ManuelaDragic/sketchingWithHardware/content/posts/pictures/applekalender.png

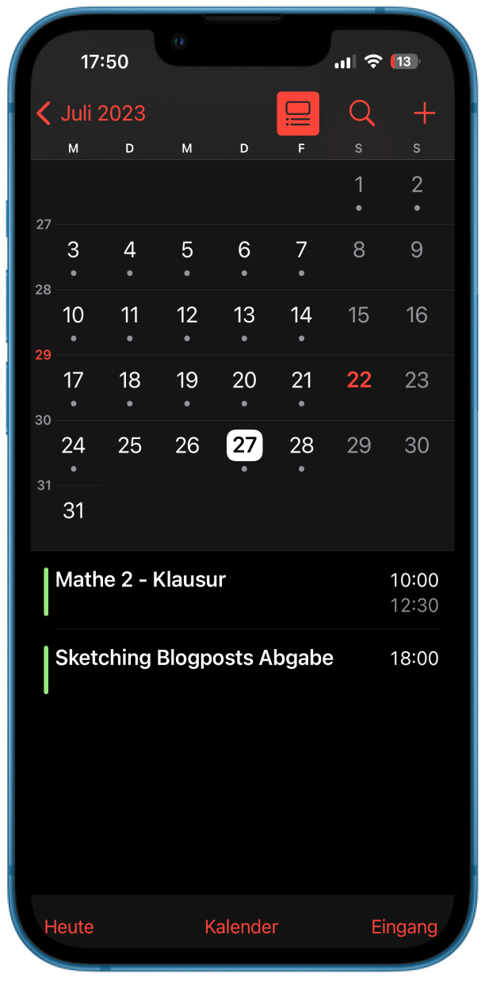
content/posts/pictures/applekalender.png
