ManuelaDragic/sketchingWithHardware/content/posts/pictures/bauteile.jpeg

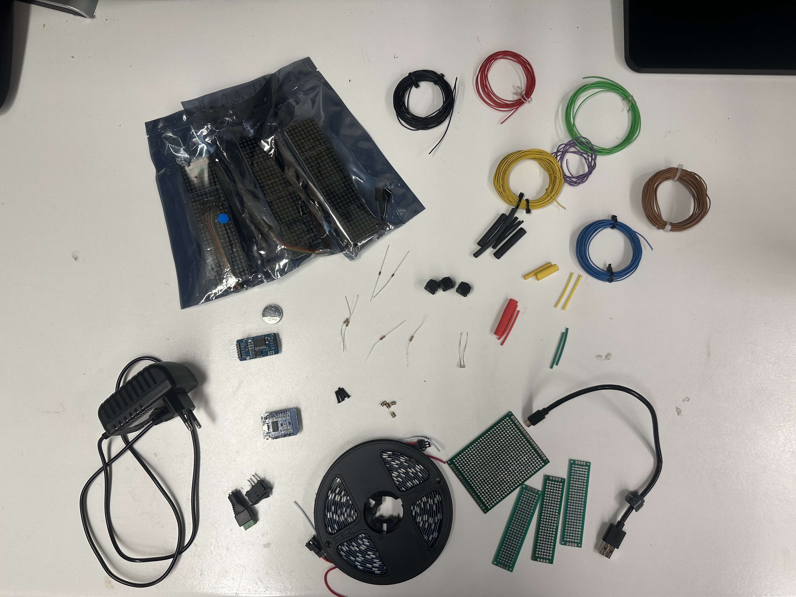
content/posts/pictures/bauteile.jpeg
