ManuelaDragic/sketchingWithHardware/content/posts/pictures/bereitstellen.png

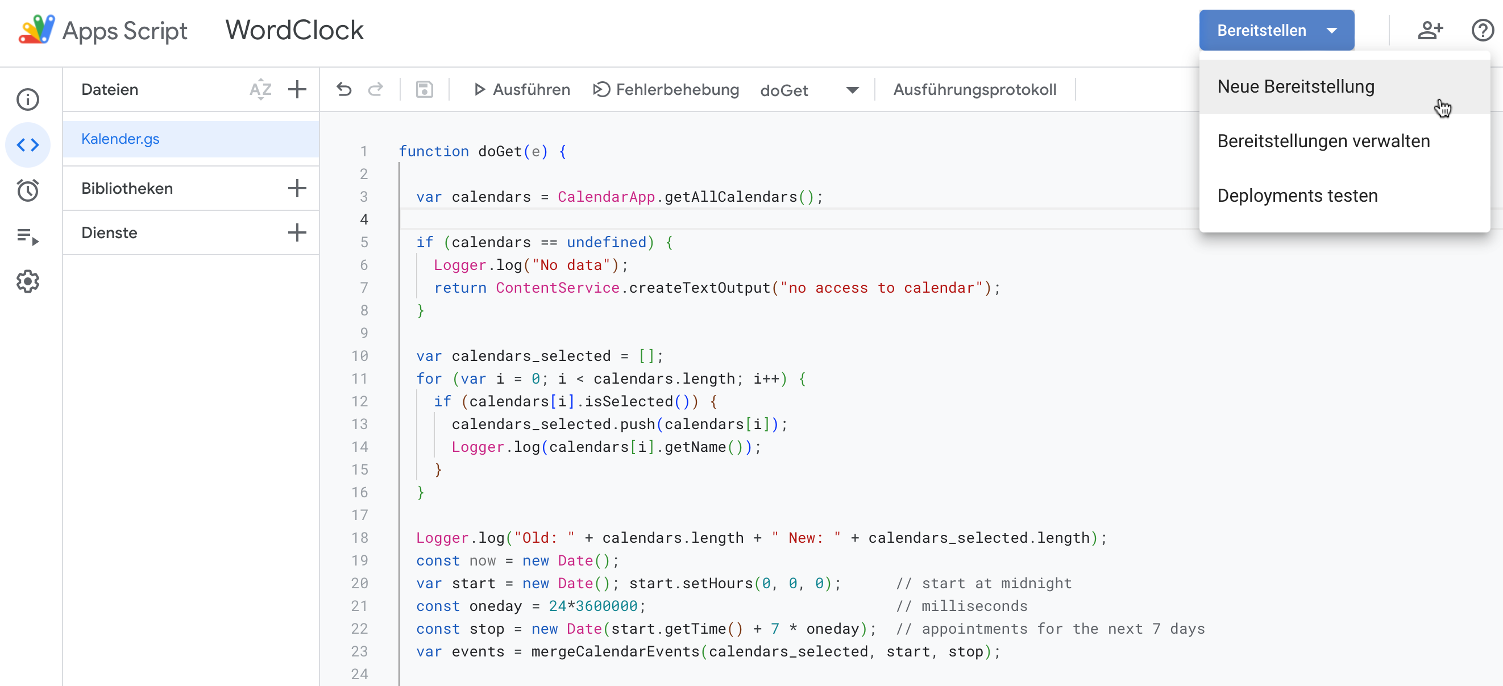
content/posts/pictures/bereitstellen.png
