ManuelaDragic/sketchingWithHardware/content/posts/pictures/boardauswahl.png

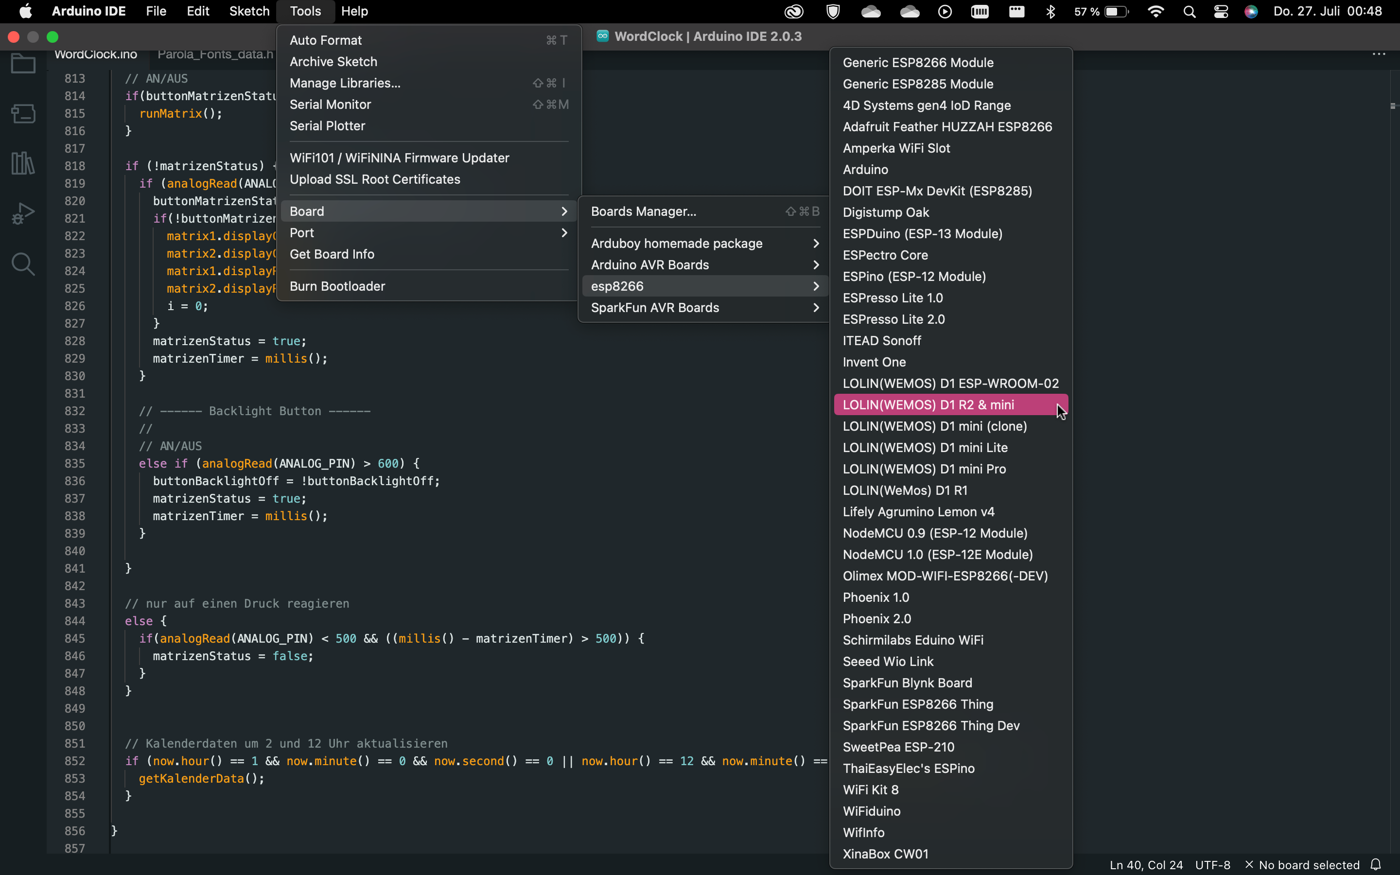
content/posts/pictures/boardauswahl.png
