ManuelaDragic/sketchingWithHardware/content/posts/pictures/boardmanager.png

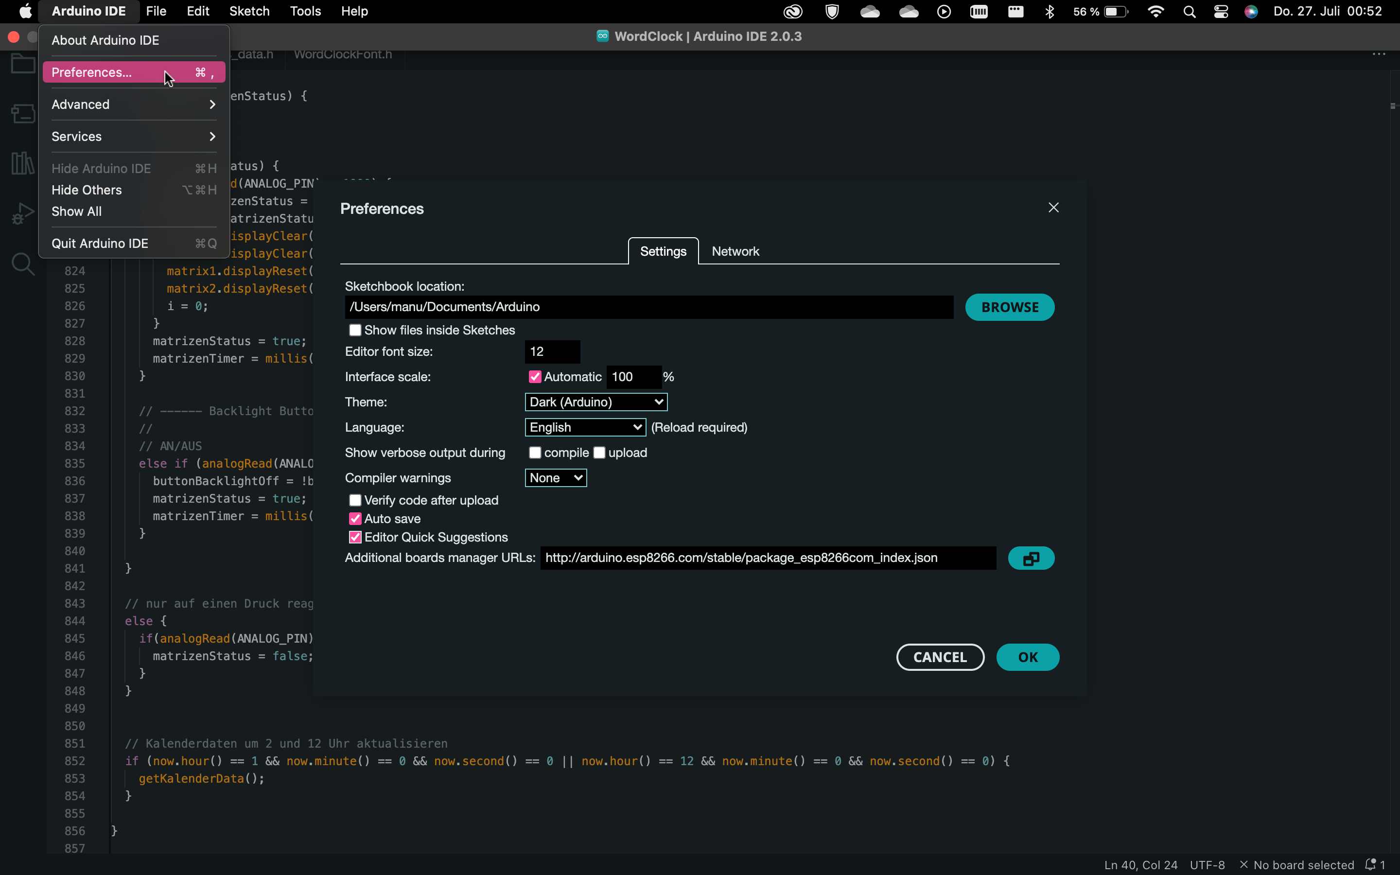
content/posts/pictures/boardmanager.png
