ManuelaDragic/sketchingWithHardware/content/posts/pictures/clock.jpeg

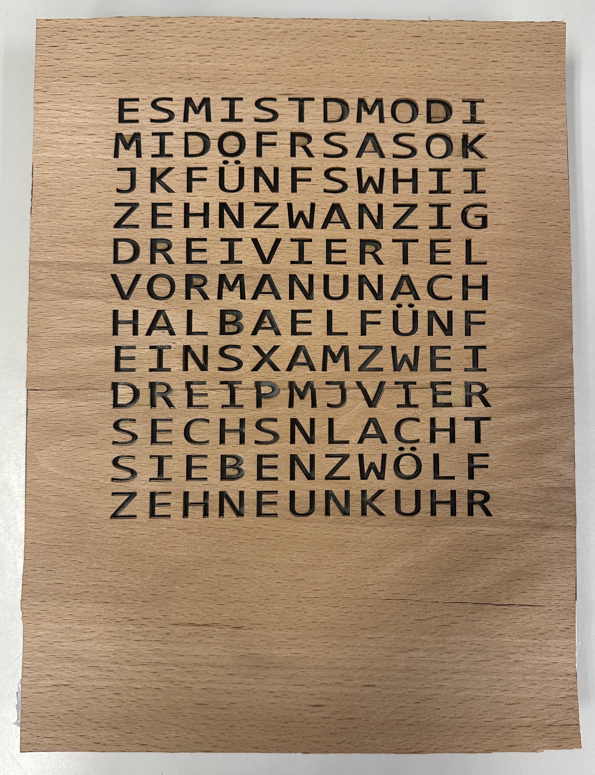
content/posts/pictures/clock.jpeg
