ManuelaDragic/sketchingWithHardware/content/posts/pictures/Code.png

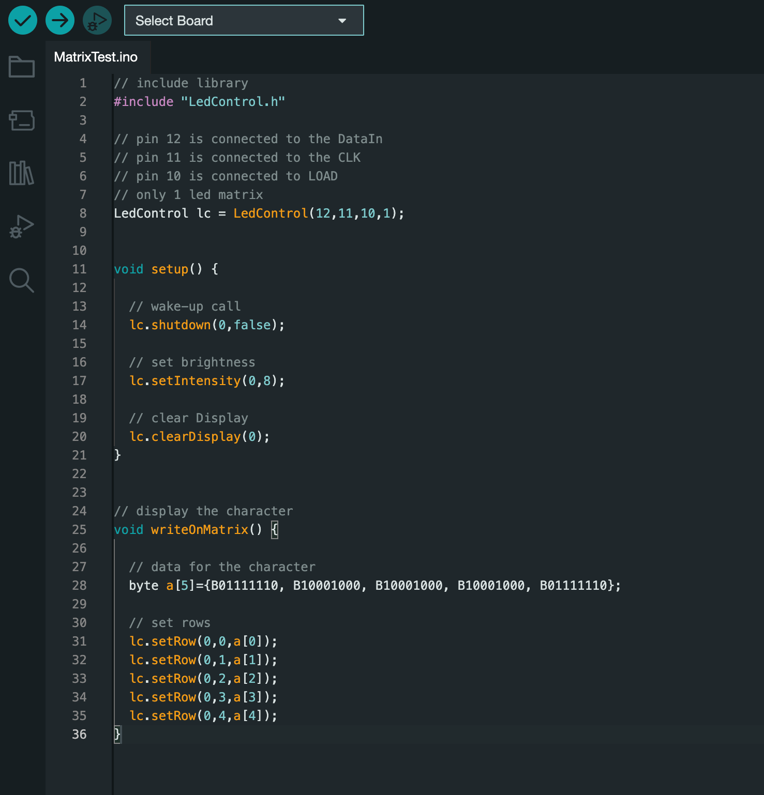
content/posts/pictures/Code.png
