ManuelaDragic/sketchingWithHardware/content/posts/pictures/druck.jpeg

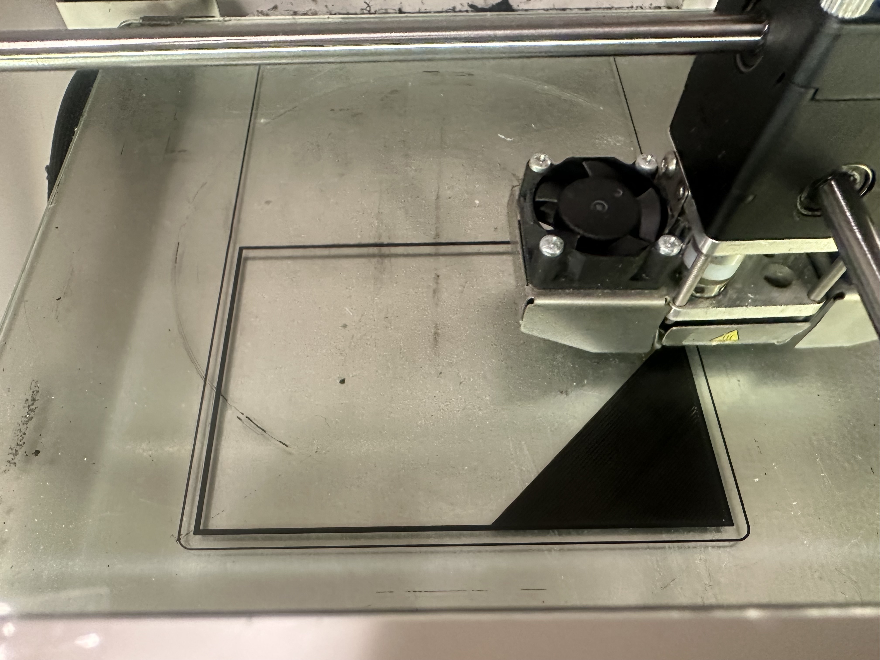
content/posts/pictures/druck.jpeg
