ManuelaDragic/sketchingWithHardware/content/posts/pictures/druck_durchsichtig.jpeg

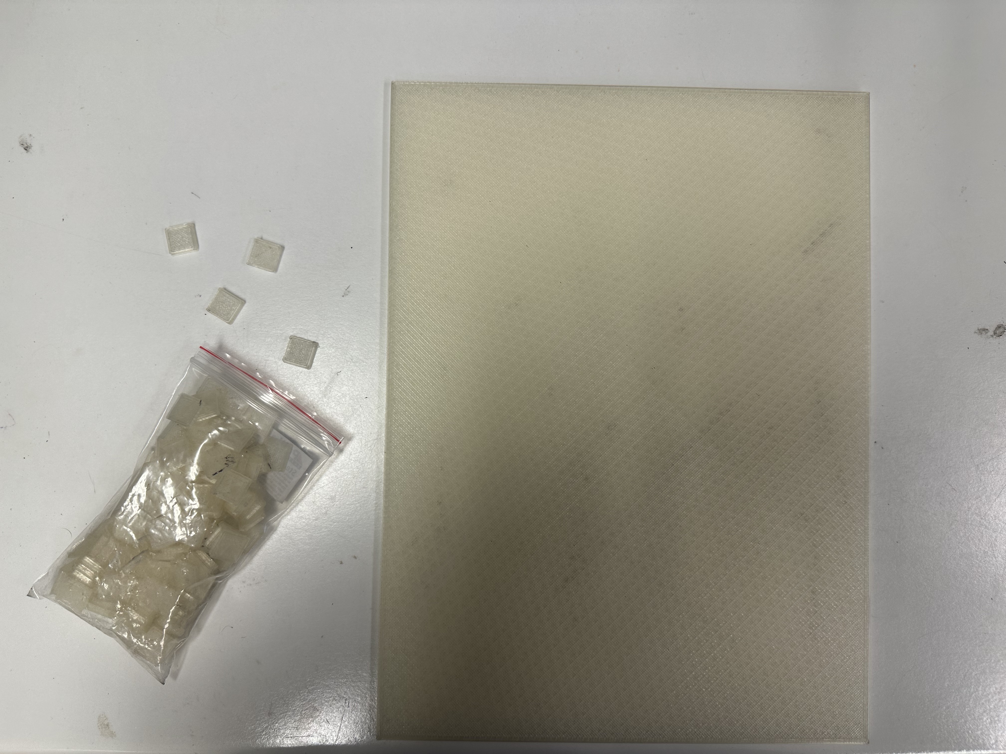
content/posts/pictures/druck_durchsichtig.jpeg
