ManuelaDragic/sketchingWithHardware/content/posts/pictures/Drucker.jpeg

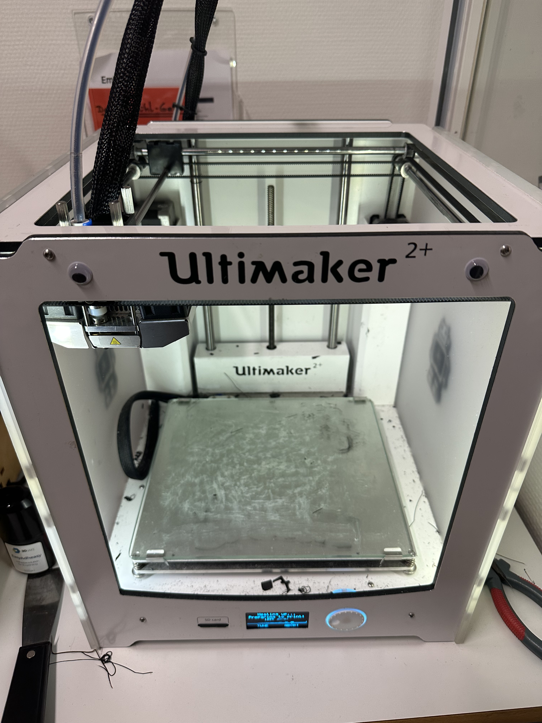
content/posts/pictures/Drucker.jpeg
