ManuelaDragic/sketchingWithHardware/content/posts/pictures/font.png

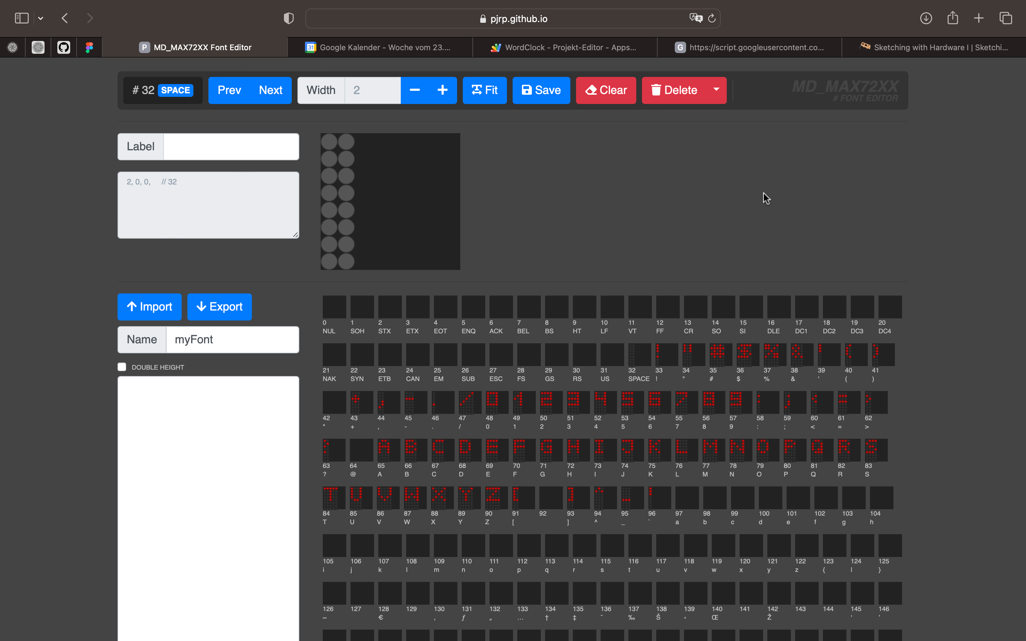
content/posts/pictures/font.png
