ManuelaDragic/sketchingWithHardware/content/posts/pictures/Gehaeuse.jpeg

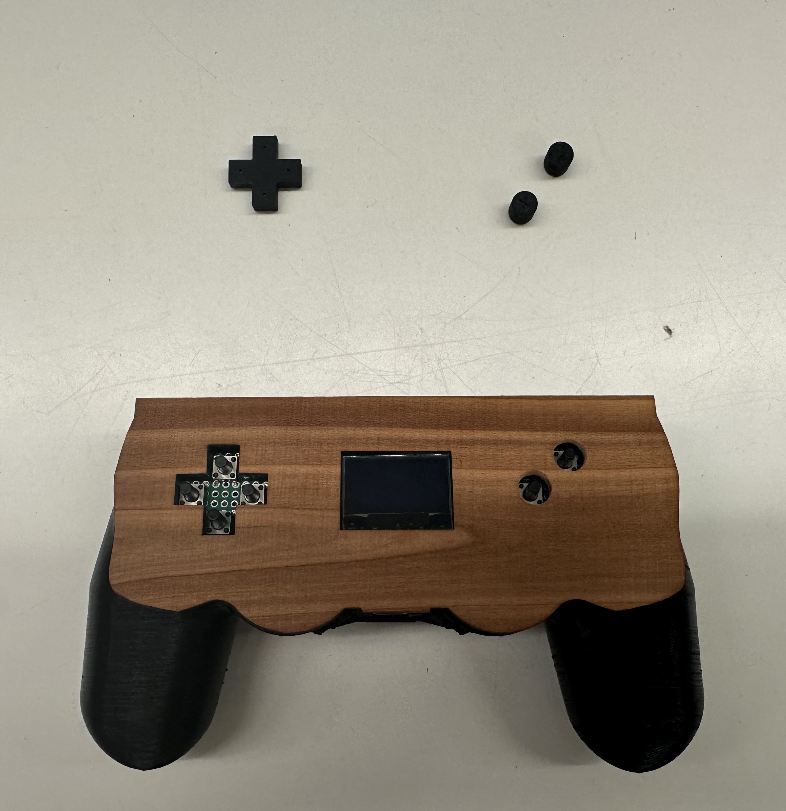
content/posts/pictures/Gehaeuse.jpeg
