ManuelaDragic/sketchingWithHardware/content/posts/pictures/Getriebe.jpeg

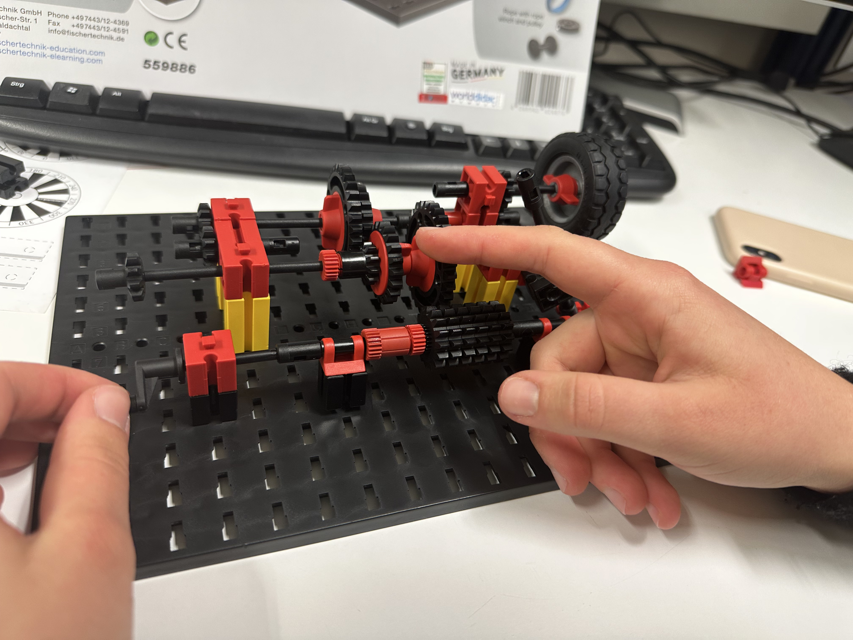
content/posts/pictures/Getriebe.jpeg
