ManuelaDragic/sketchingWithHardware/content/posts/pictures/hinten.png

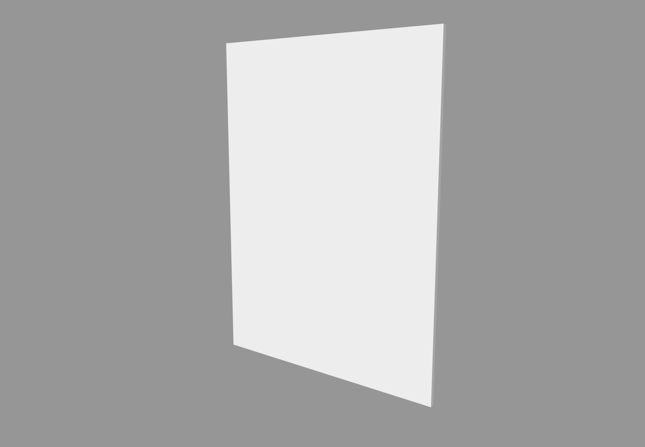
content/posts/pictures/hinten.png
