ManuelaDragic/sketchingWithHardware/content/posts/pictures/Interrupts.png

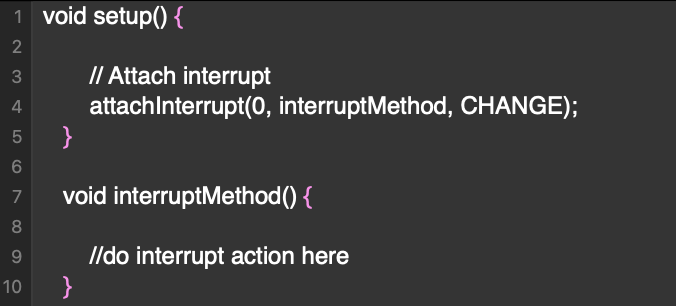
content/posts/pictures/Interrupts.png
