ManuelaDragic/sketchingWithHardware/content/posts/pictures/kalender_abonnieren.png

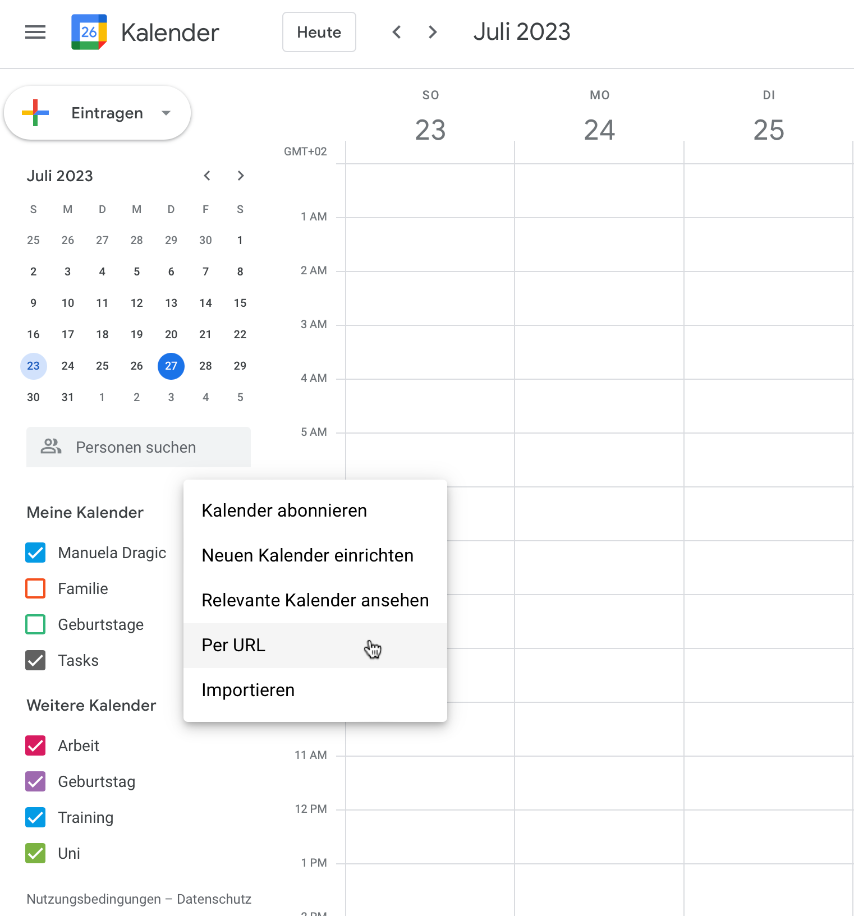
content/posts/pictures/kalender_abonnieren.png
