ManuelaDragic/sketchingWithHardware/content/posts/pictures/kalender_desktop.png

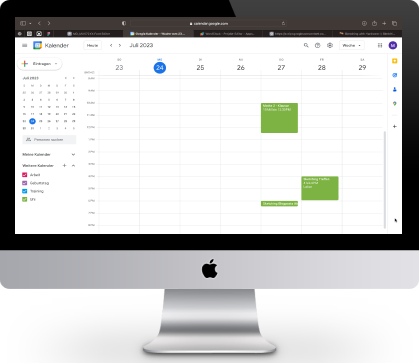
content/posts/pictures/kalender_desktop.png
