ManuelaDragic/sketchingWithHardware/content/posts/pictures/kalenderdaten2.png

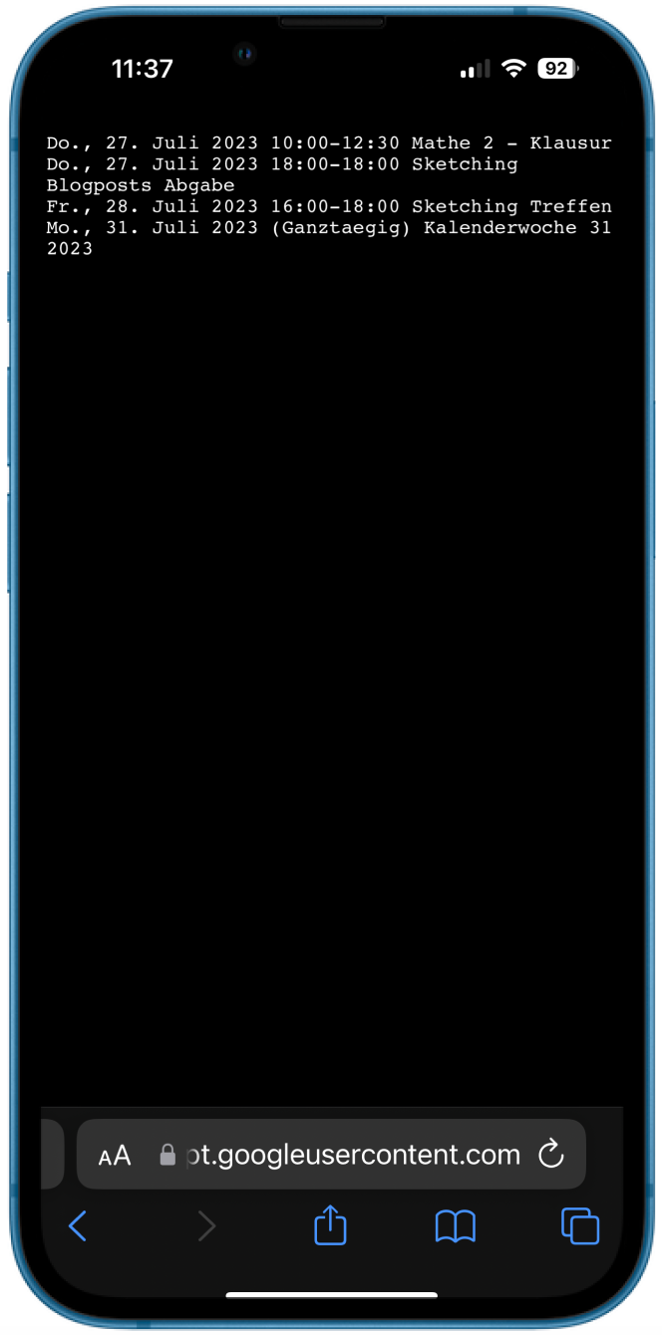
content/posts/pictures/kalenderdaten2.png
