ManuelaDragic/sketchingWithHardware/content/posts/pictures/kalenderdaten_desktop.png

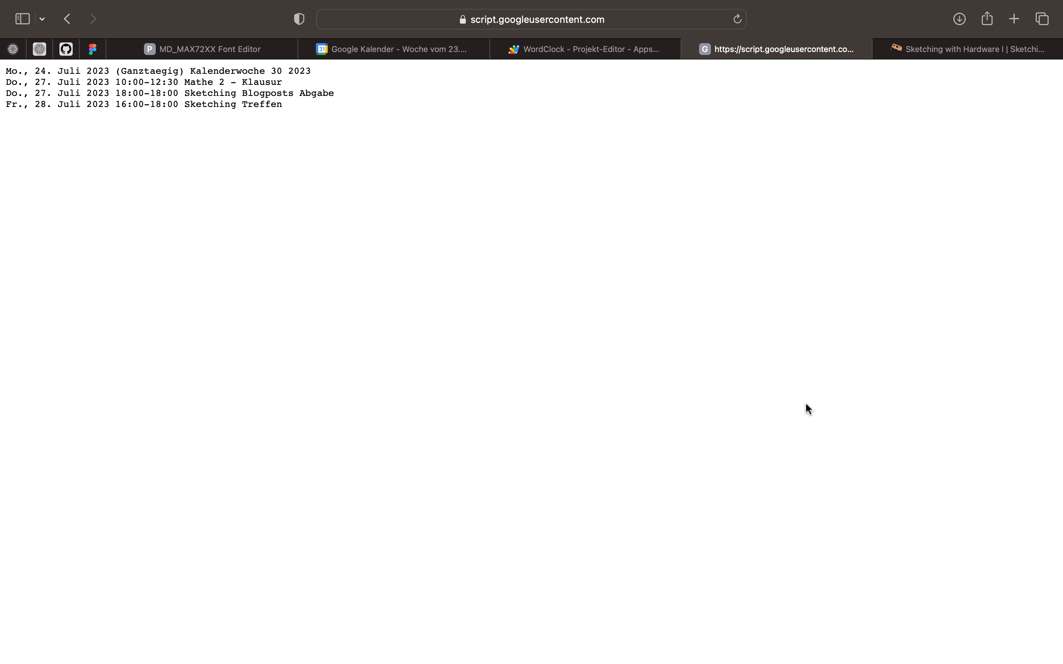
content/posts/pictures/kalenderdaten_desktop.png
