ManuelaDragic/sketchingWithHardware/content/posts/pictures/led_halterung.jpeg

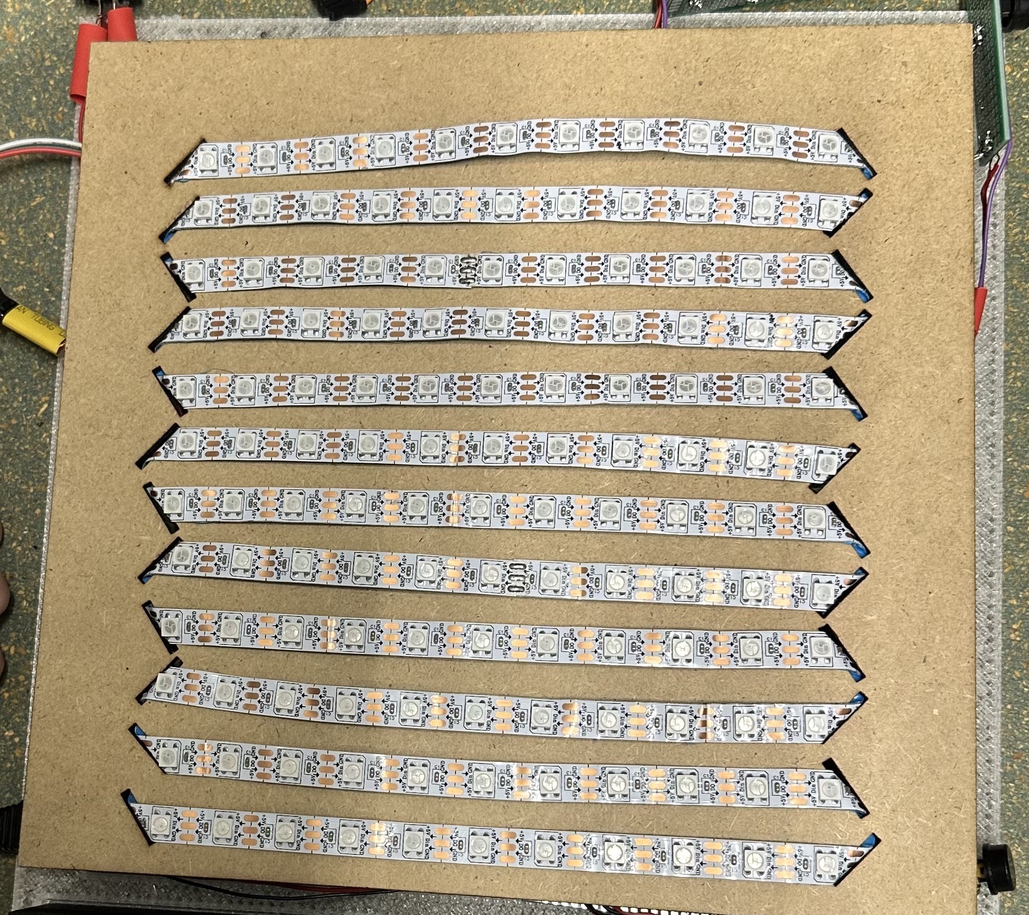
content/posts/pictures/led_halterung.jpeg
