ManuelaDragic/sketchingWithHardware/content/posts/pictures/libraries.png

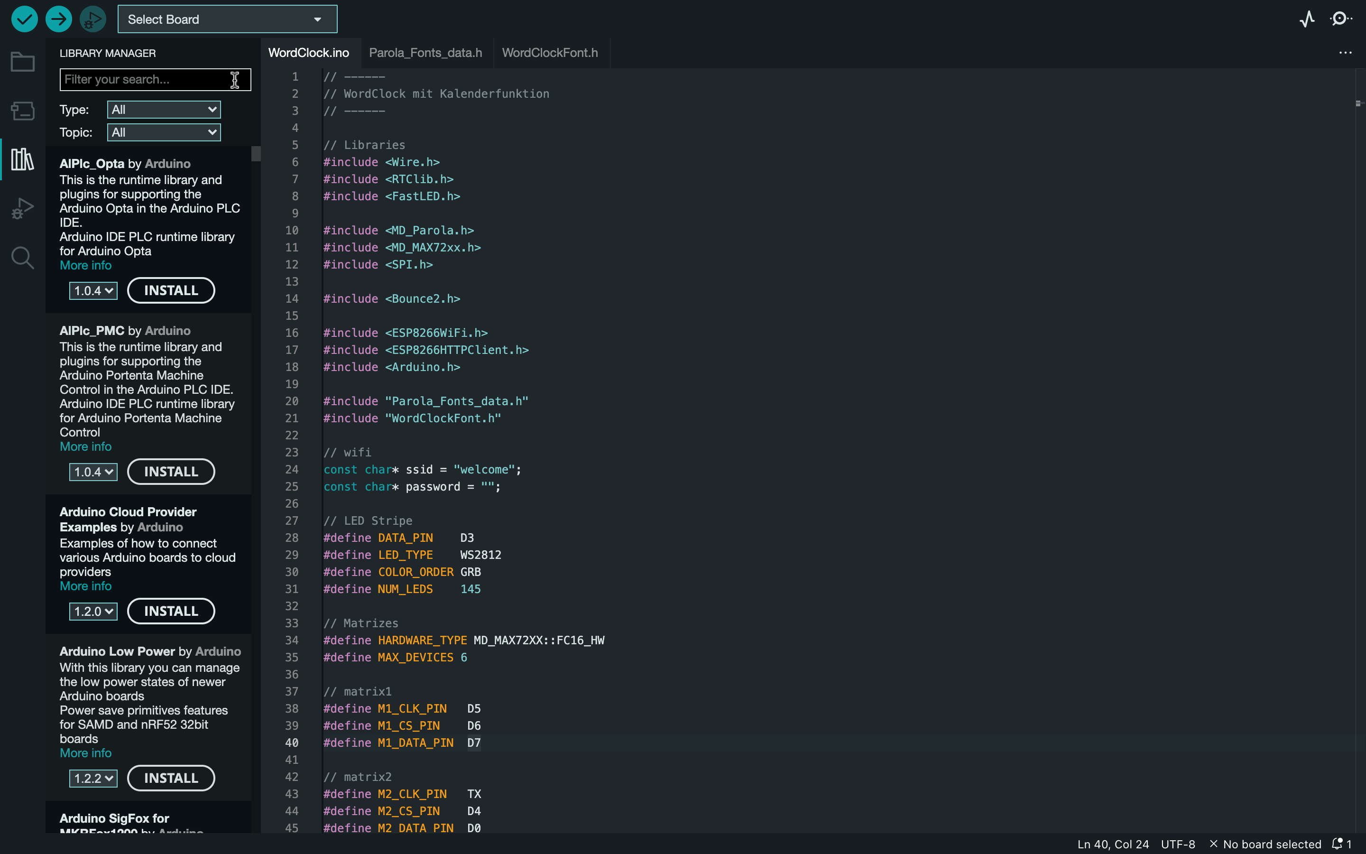
content/posts/pictures/libraries.png
