ManuelaDragic/sketchingWithHardware/content/posts/pictures/Lightburn.png

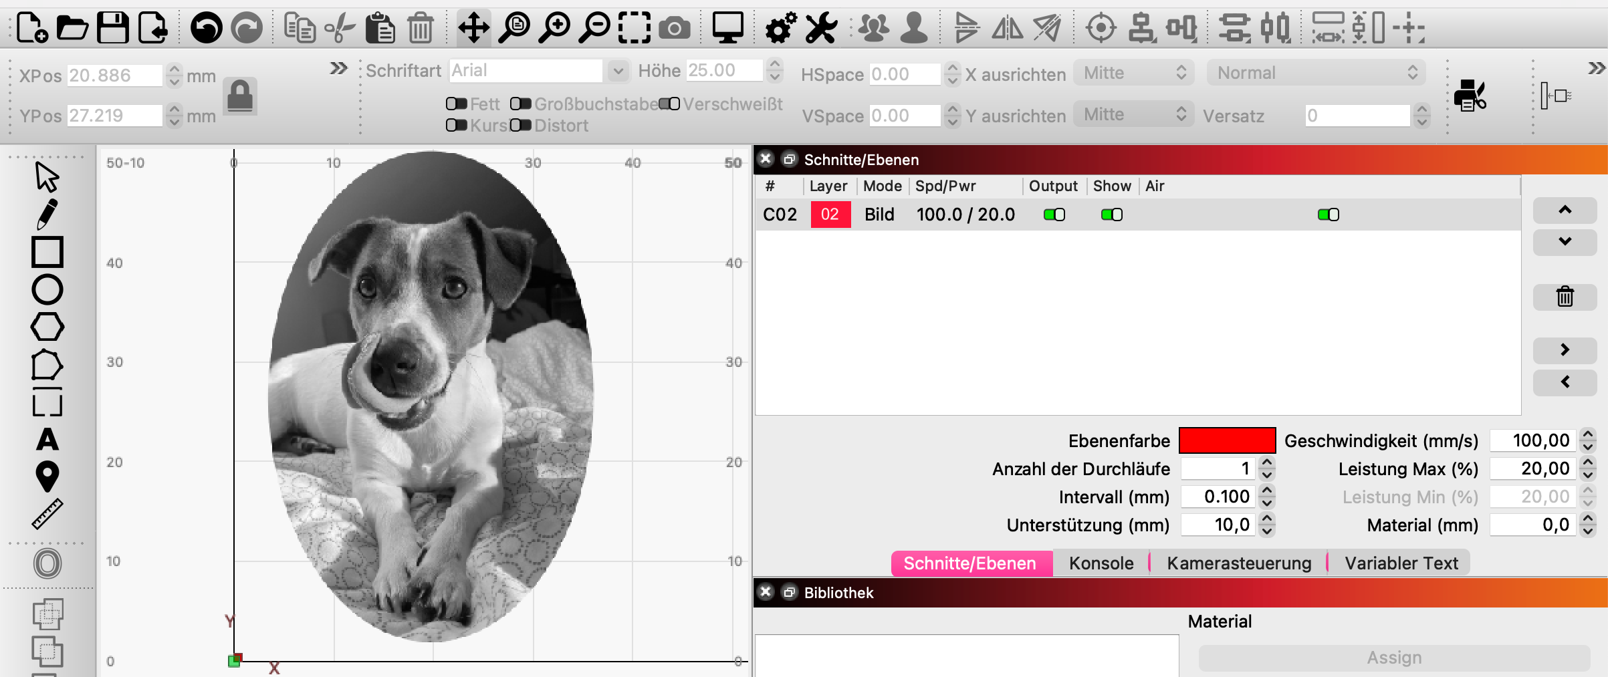
content/posts/pictures/Lightburn.png
