ManuelaDragic/sketchingWithHardware/content/posts/pictures/link.png

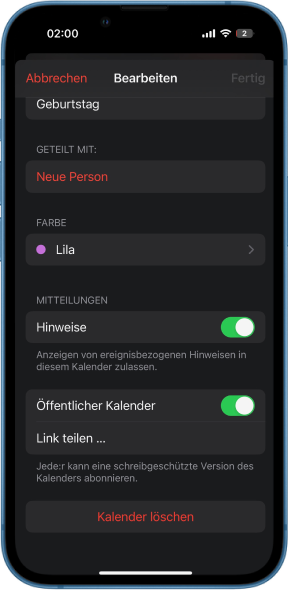
content/posts/pictures/link.png
