ManuelaDragic/sketchingWithHardware/content/posts/pictures/loeten1.png

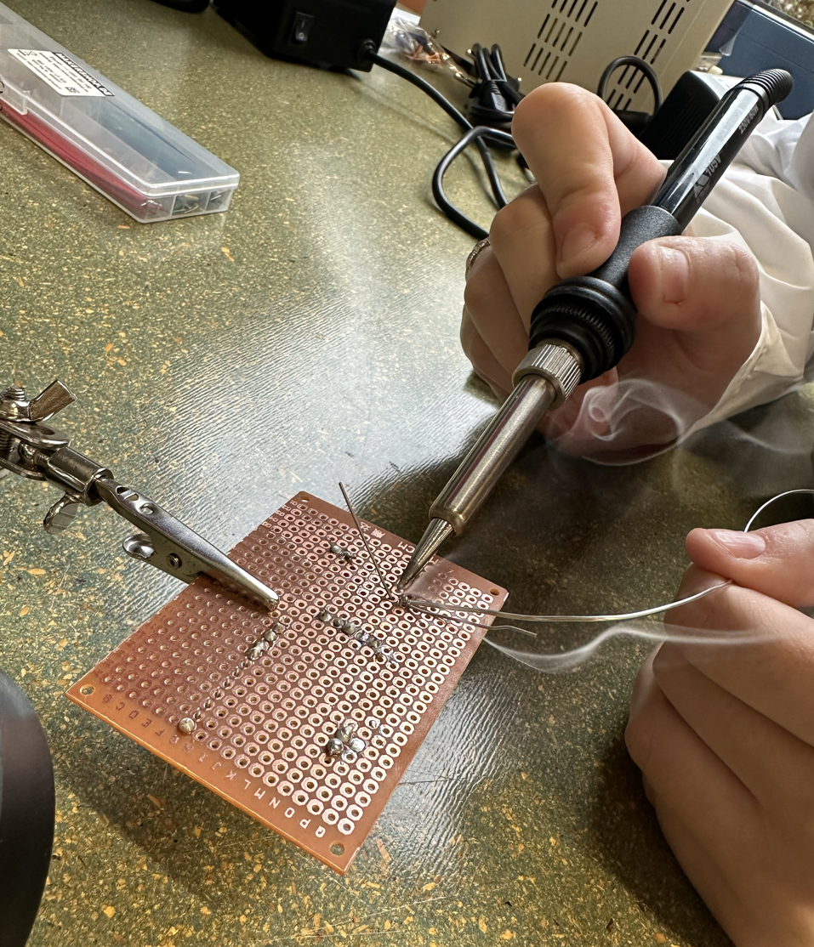
content/posts/pictures/loeten1.png
