ManuelaDragic/sketchingWithHardware/content/posts/pictures/loeten2.png

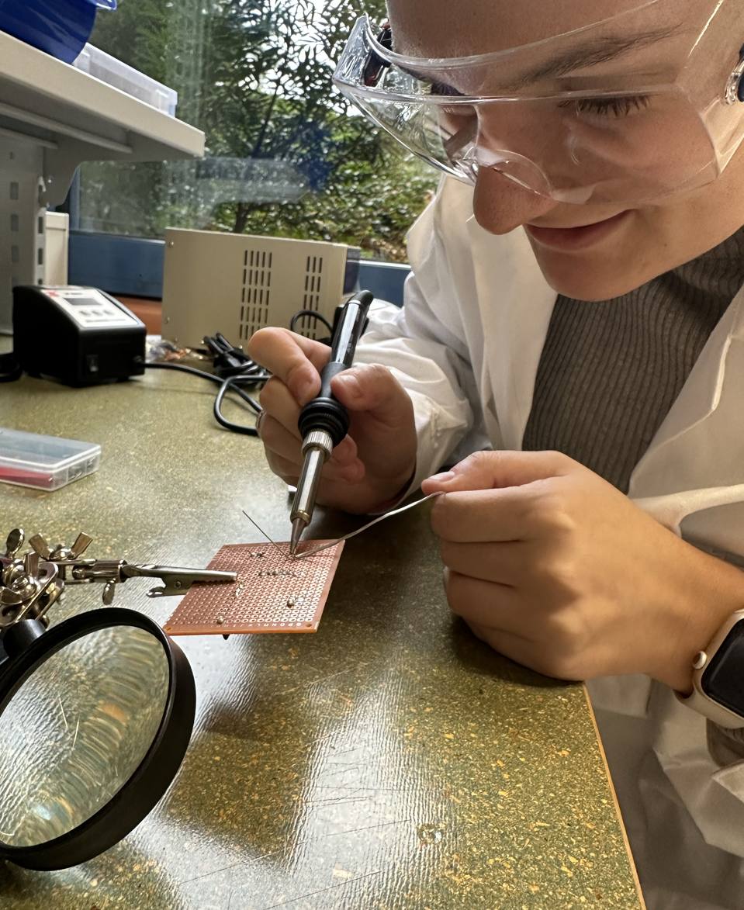
content/posts/pictures/loeten2.png
