ManuelaDragic/sketchingWithHardware/content/posts/pictures/loetplan.jpg

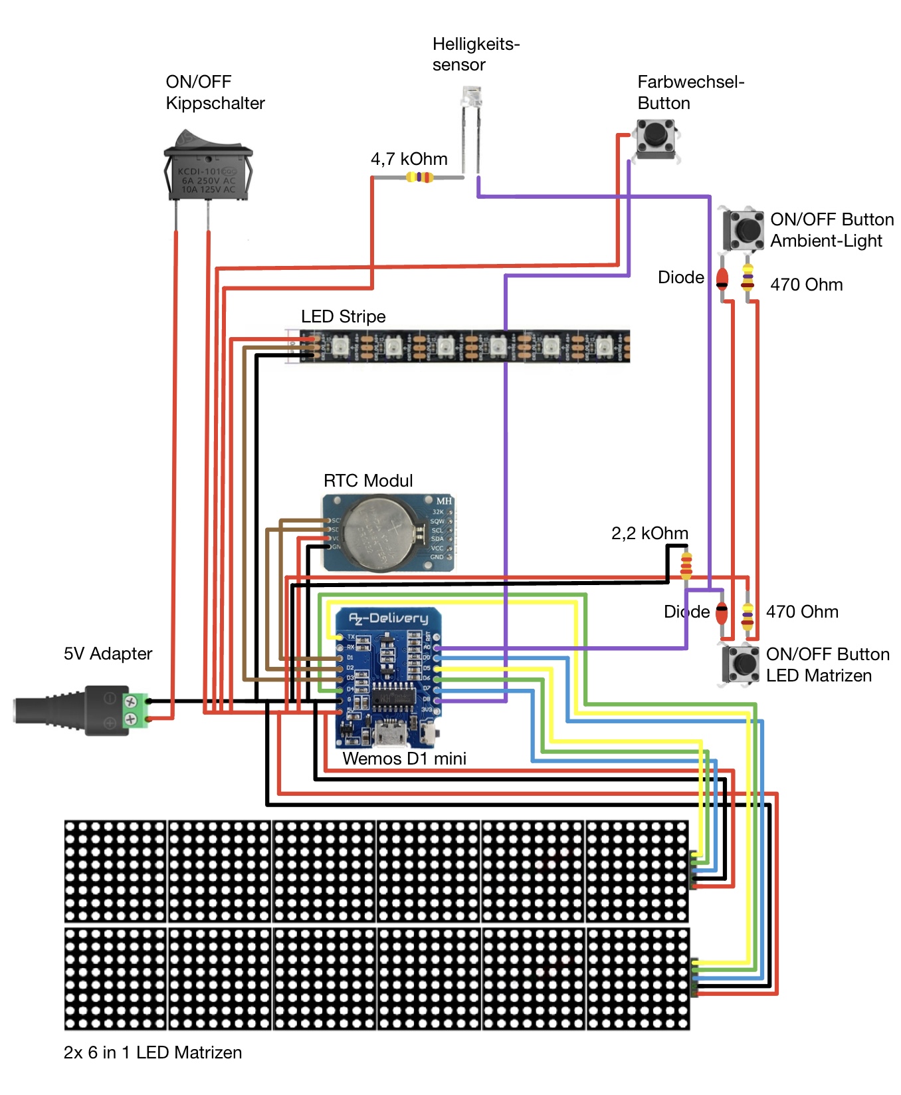
content/posts/pictures/loetplan.jpg
