ManuelaDragic/sketchingWithHardware/content/posts/pictures/loetzubehoer.png

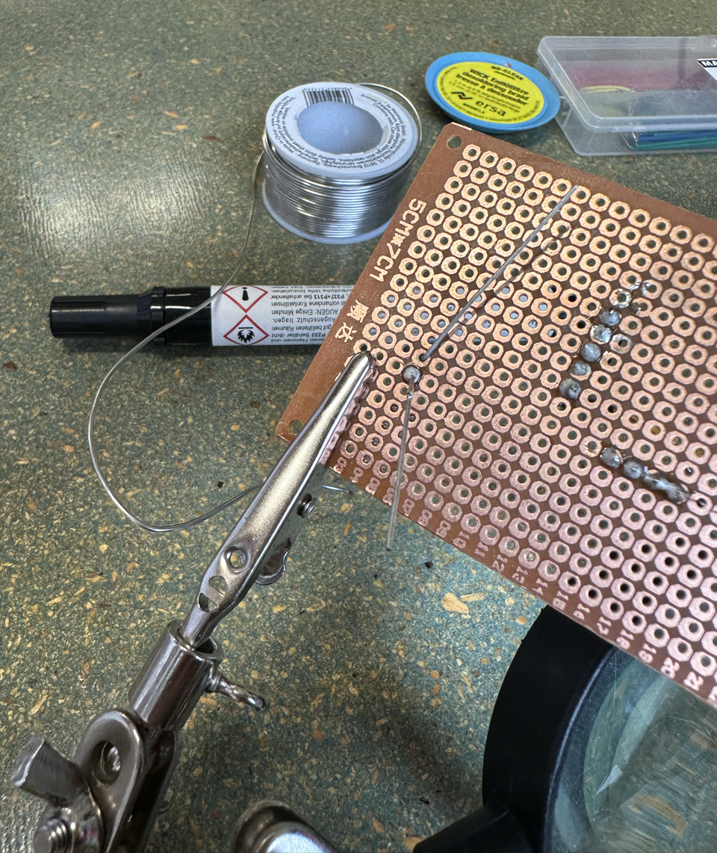
content/posts/pictures/loetzubehoer.png
