ManuelaDragic/sketchingWithHardware/content/posts/pictures/matrizenhalterung.png

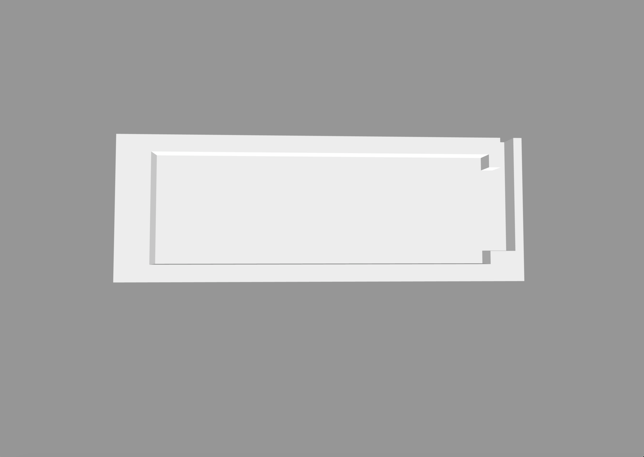
content/posts/pictures/matrizenhalterung.png
