ManuelaDragic/sketchingWithHardware/content/posts/pictures/Messung.png

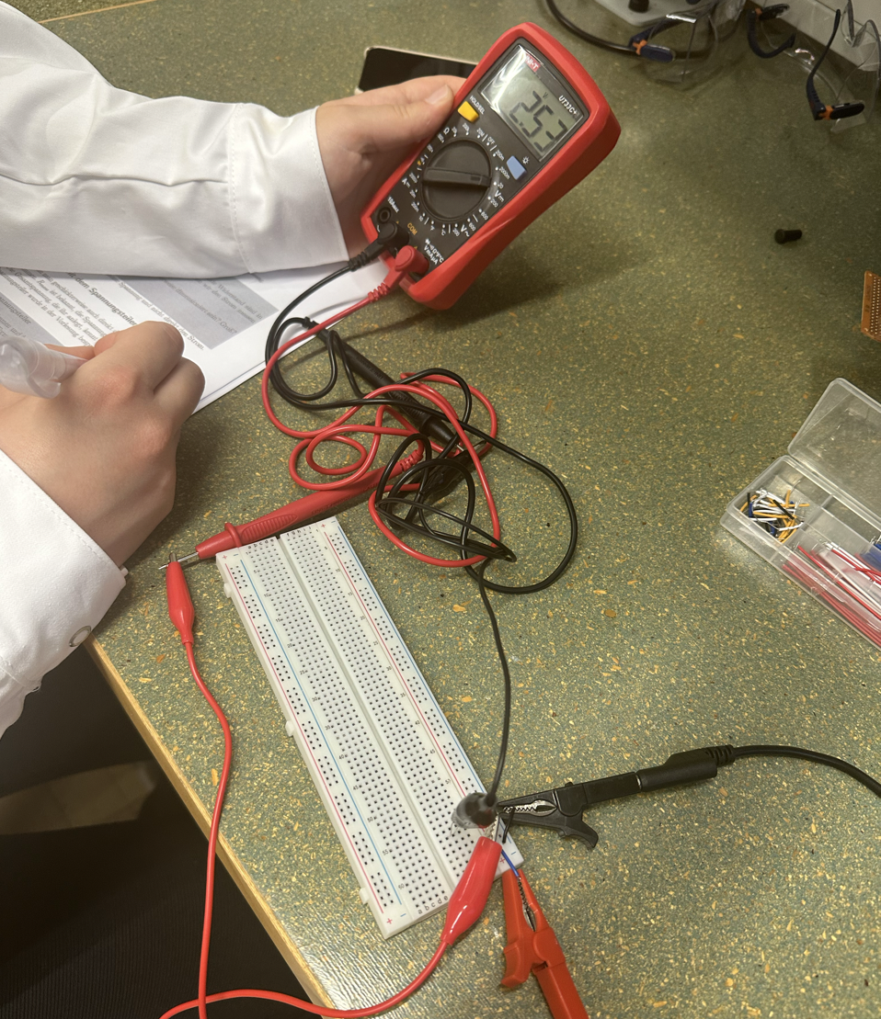
content/posts/pictures/Messung.png
