ManuelaDragic/sketchingWithHardware/content/posts/pictures/Messwerte.png

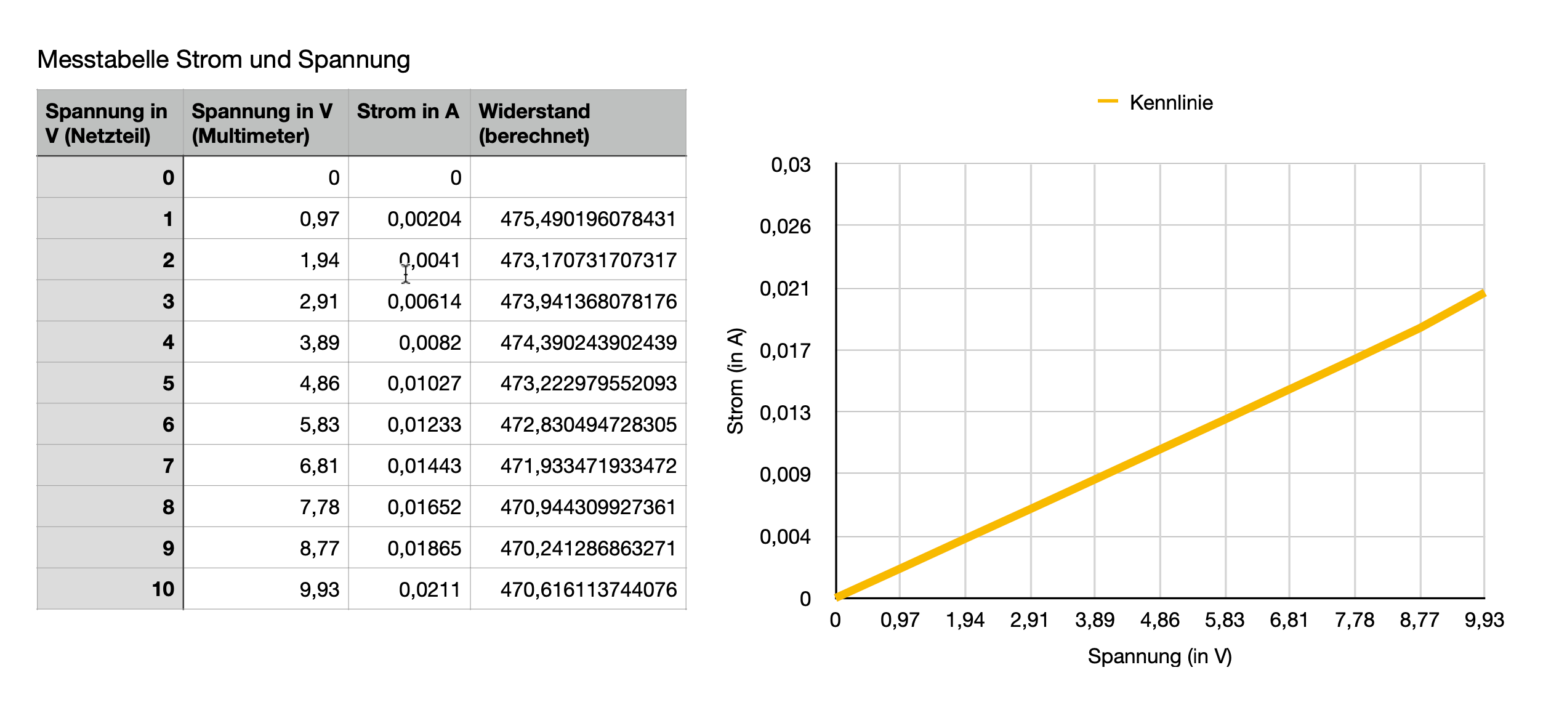
content/posts/pictures/Messwerte.png
