ManuelaDragic/sketchingWithHardware/content/posts/pictures/neuesProjekt.png

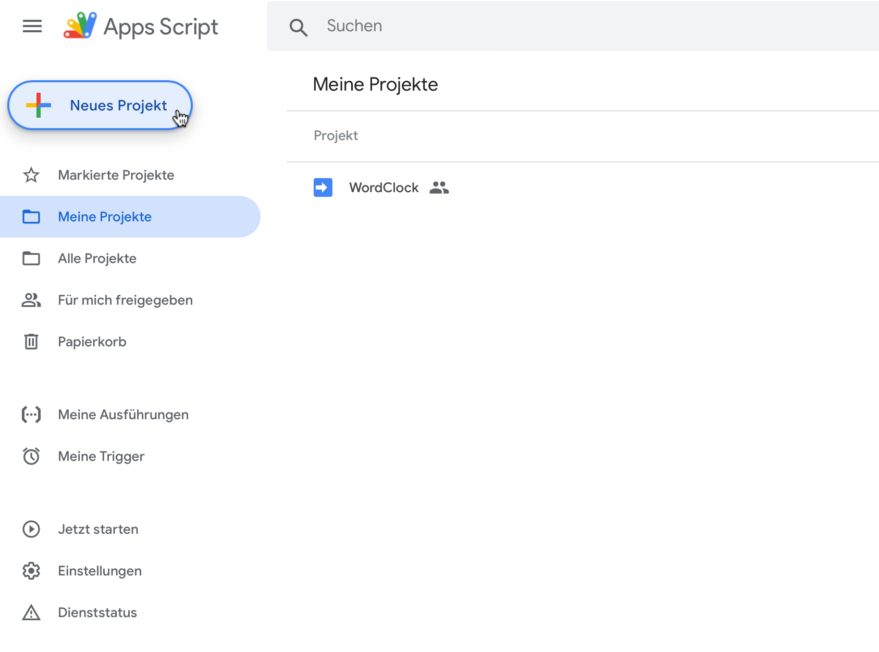
content/posts/pictures/neuesProjekt.png
