ManuelaDragic/sketchingWithHardware/content/posts/pictures/offen.jpeg

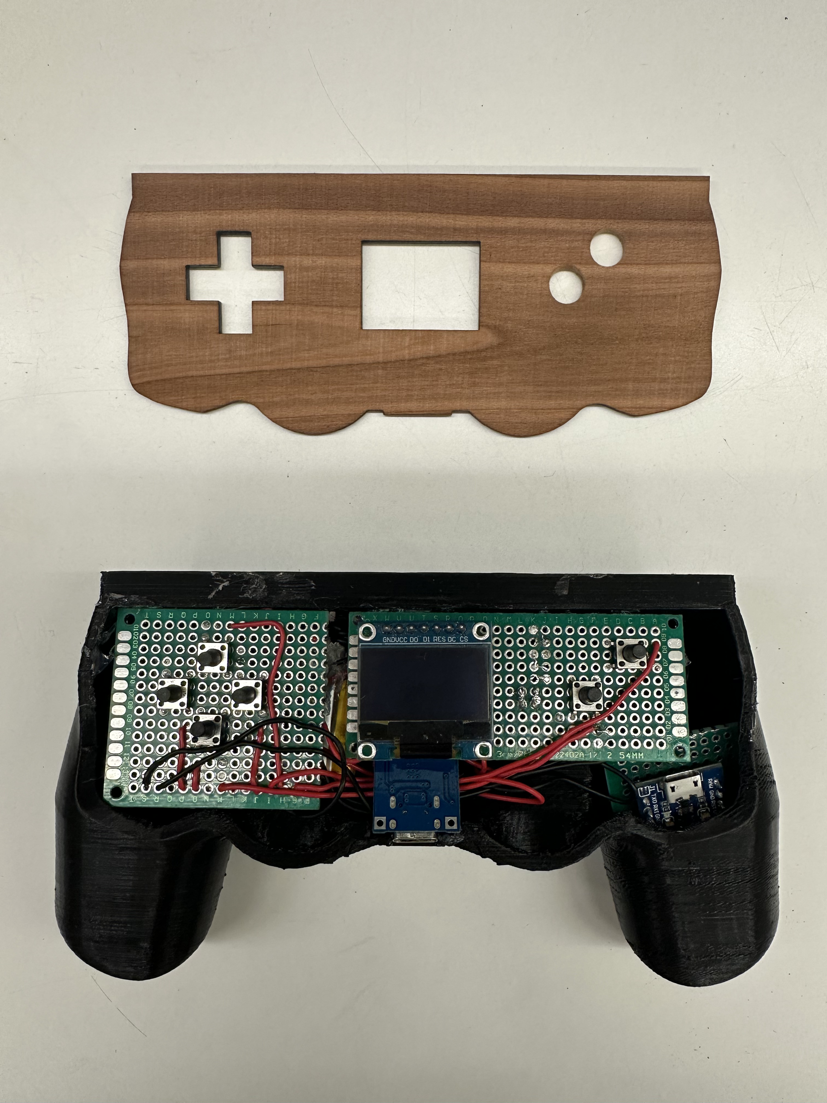
content/posts/pictures/offen.jpeg
