ManuelaDragic/sketchingWithHardware/content/posts/pictures/Planetengetriebe.jpeg

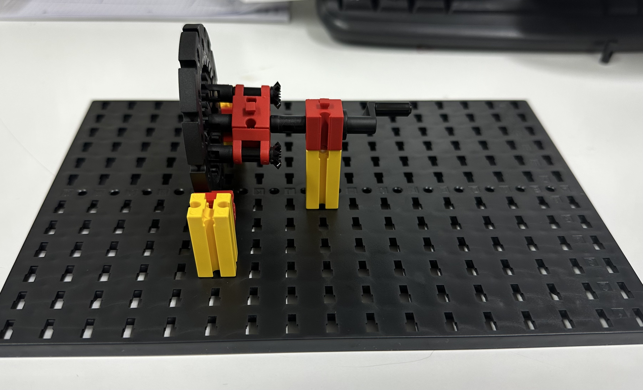
content/posts/pictures/Planetengetriebe.jpeg
