ManuelaDragic/sketchingWithHardware/content/posts/pictures/platte.jpeg

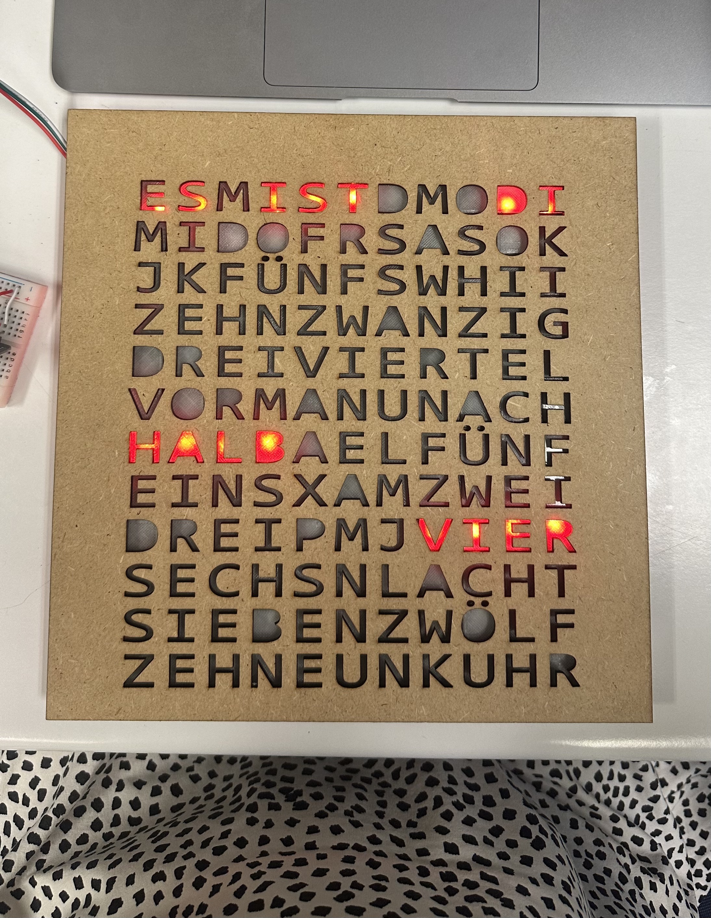
content/posts/pictures/platte.jpeg
