ManuelaDragic/sketchingWithHardware/content/posts/pictures/projektpitch2.png

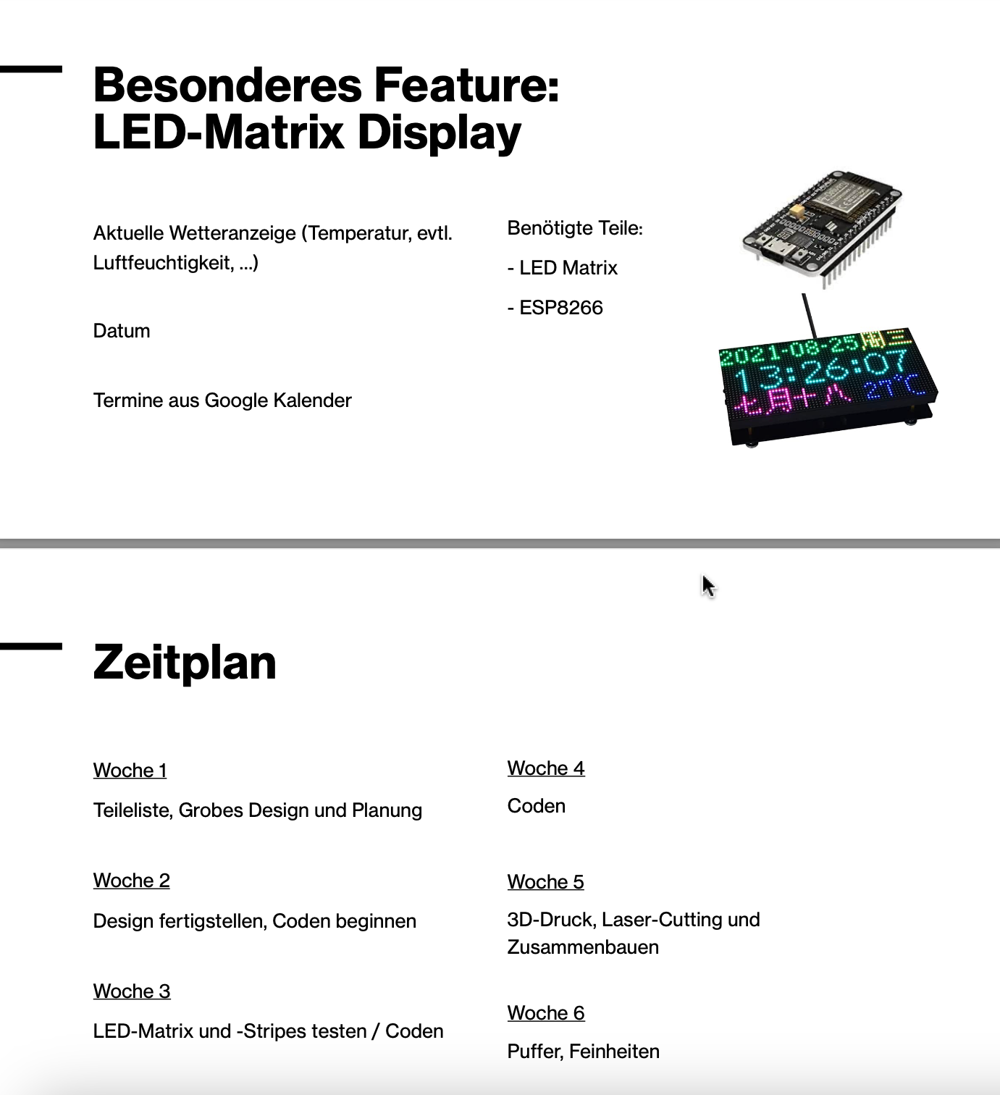
content/posts/pictures/projektpitch2.png
