ManuelaDragic/sketchingWithHardware/content/posts/pictures/rahmen.png

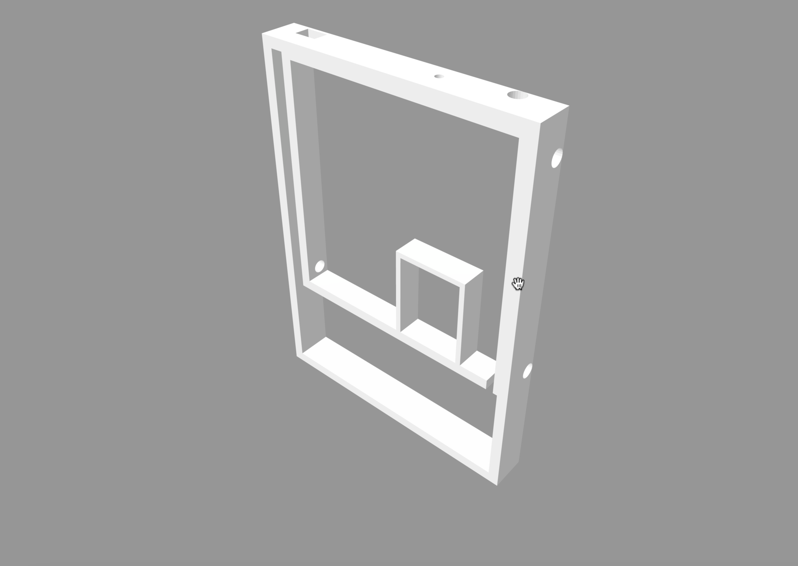
content/posts/pictures/rahmen.png
