ManuelaDragic/sketchingWithHardware/content/posts/pictures/Rahmen_links(neu).jpeg

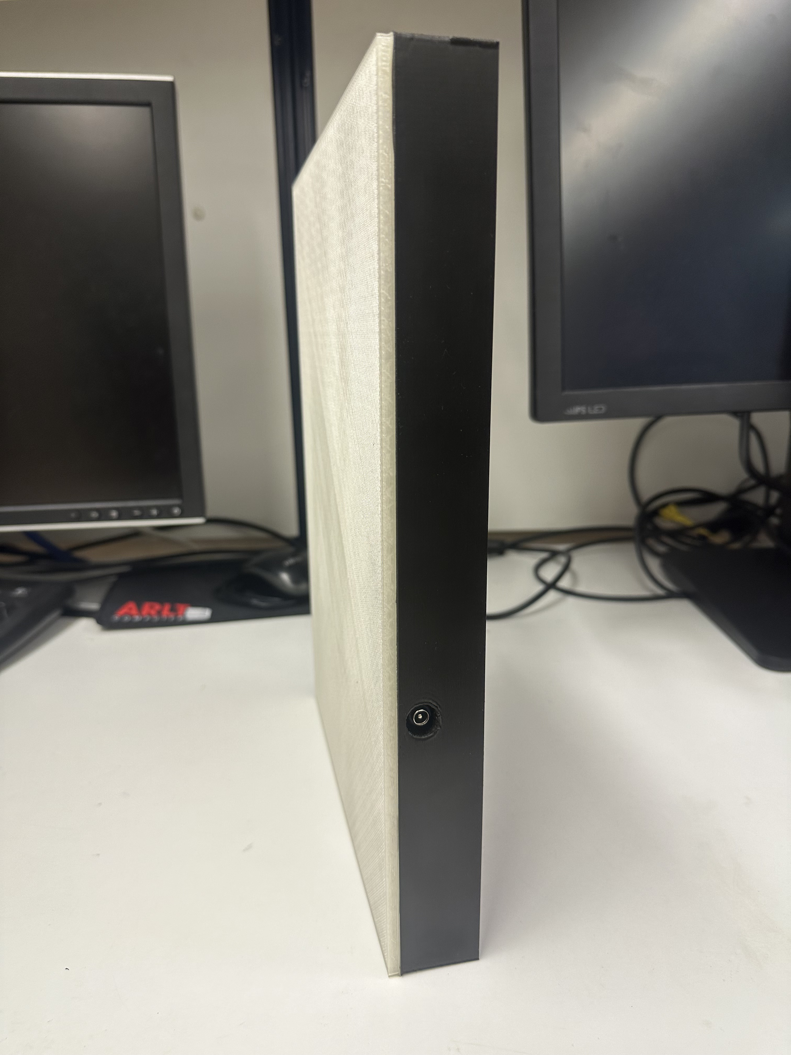
content/posts/pictures/Rahmen_links(neu).jpeg
