ManuelaDragic/sketchingWithHardware/content/posts/pictures/Rahmen_oben(alt).jpeg

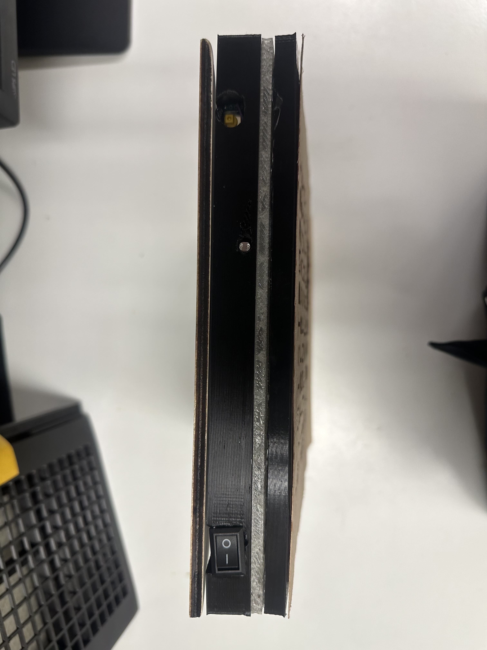
content/posts/pictures/Rahmen_oben(alt).jpeg
