ManuelaDragic/sketchingWithHardware/content/posts/pictures/Rahmen_oben(neu).jpeg

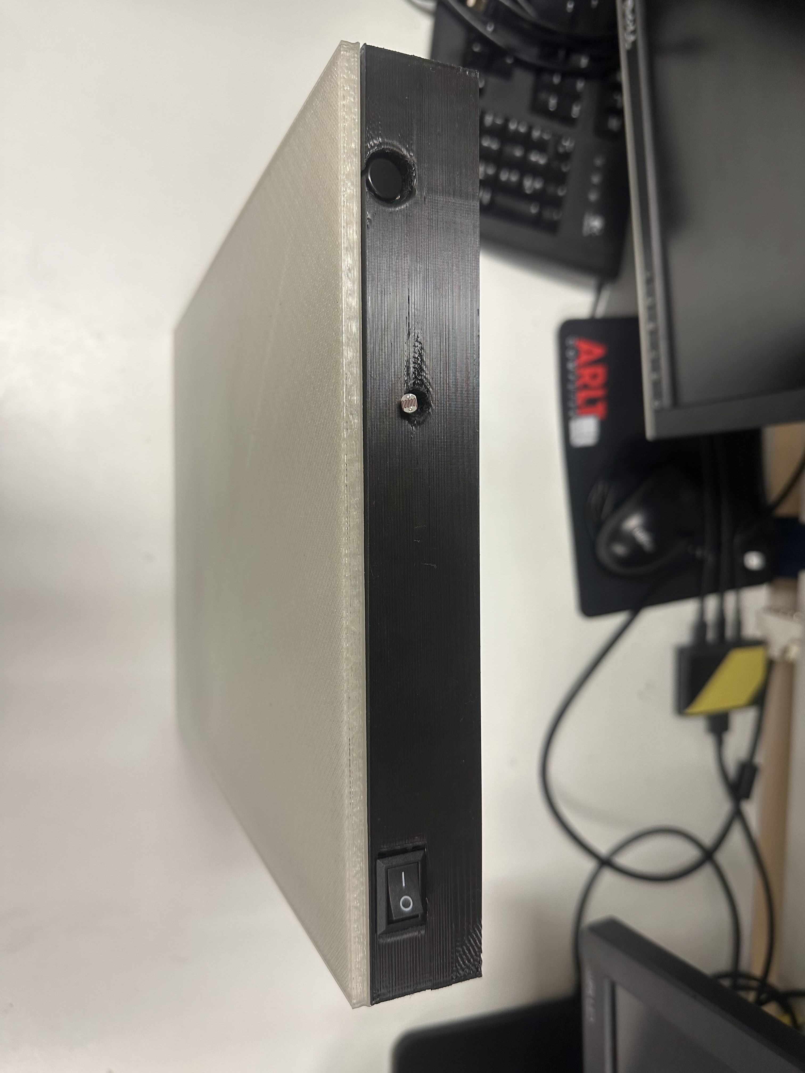
content/posts/pictures/Rahmen_oben(neu).jpeg
