ManuelaDragic/sketchingWithHardware/content/posts/pictures/Rahmen_rechts(alt).jpeg

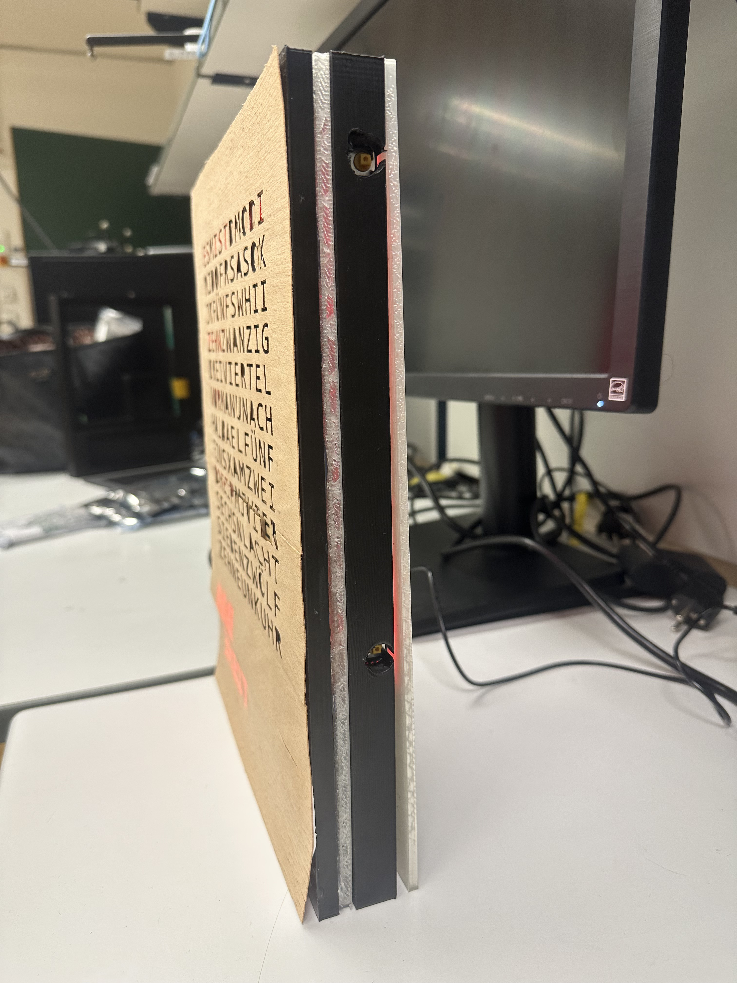
content/posts/pictures/Rahmen_rechts(alt).jpeg
