ManuelaDragic/sketchingWithHardware/content/posts/pictures/Rahmen_rechts(neu).jpeg

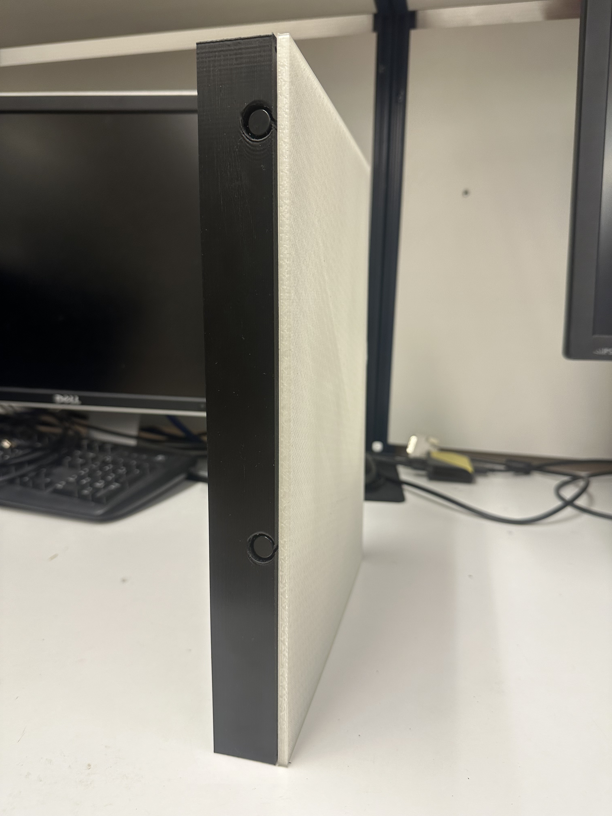
content/posts/pictures/Rahmen_rechts(neu).jpeg
