ManuelaDragic/sketchingWithHardware/content/posts/pictures/raster.JPG

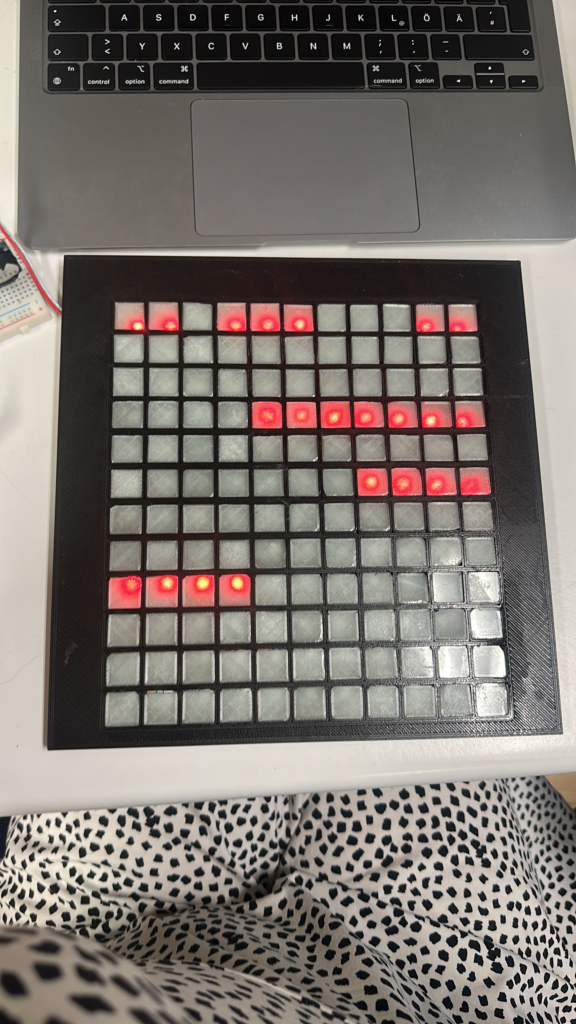
content/posts/pictures/raster.JPG
