ManuelaDragic/sketchingWithHardware/content/posts/pictures/raster.png

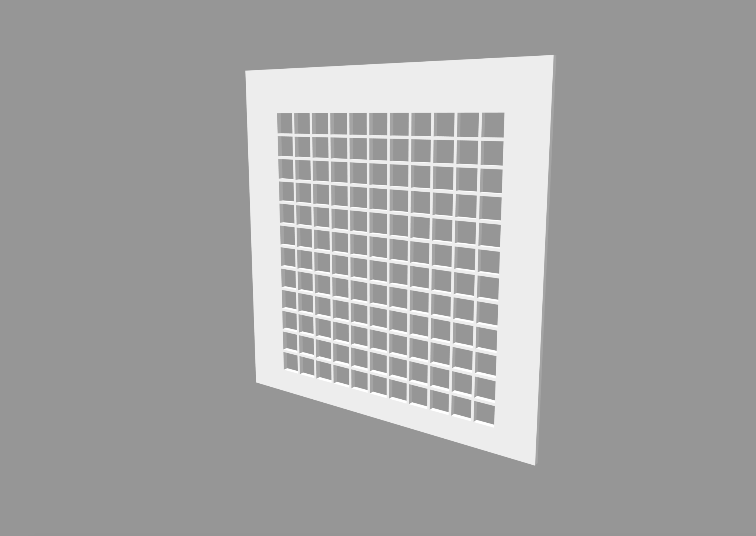
content/posts/pictures/raster.png
