ManuelaDragic/sketchingWithHardware/content/posts/pictures/raster_innen.png

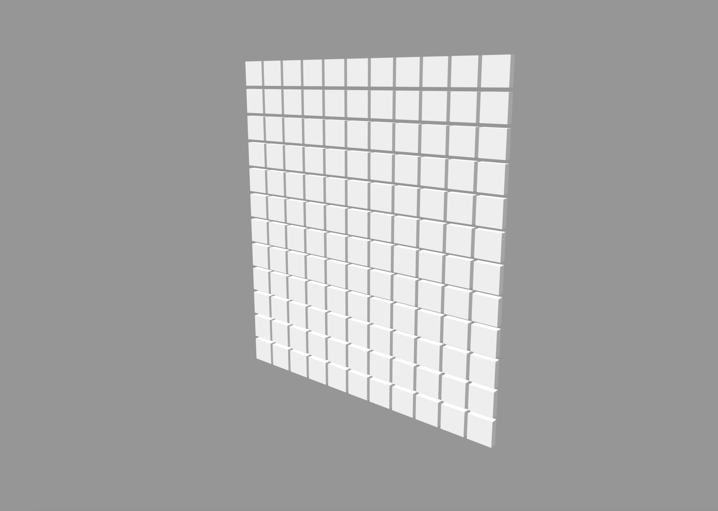
content/posts/pictures/raster_innen.png
