ManuelaDragic/sketchingWithHardware/content/posts/pictures/Schaltplan.png

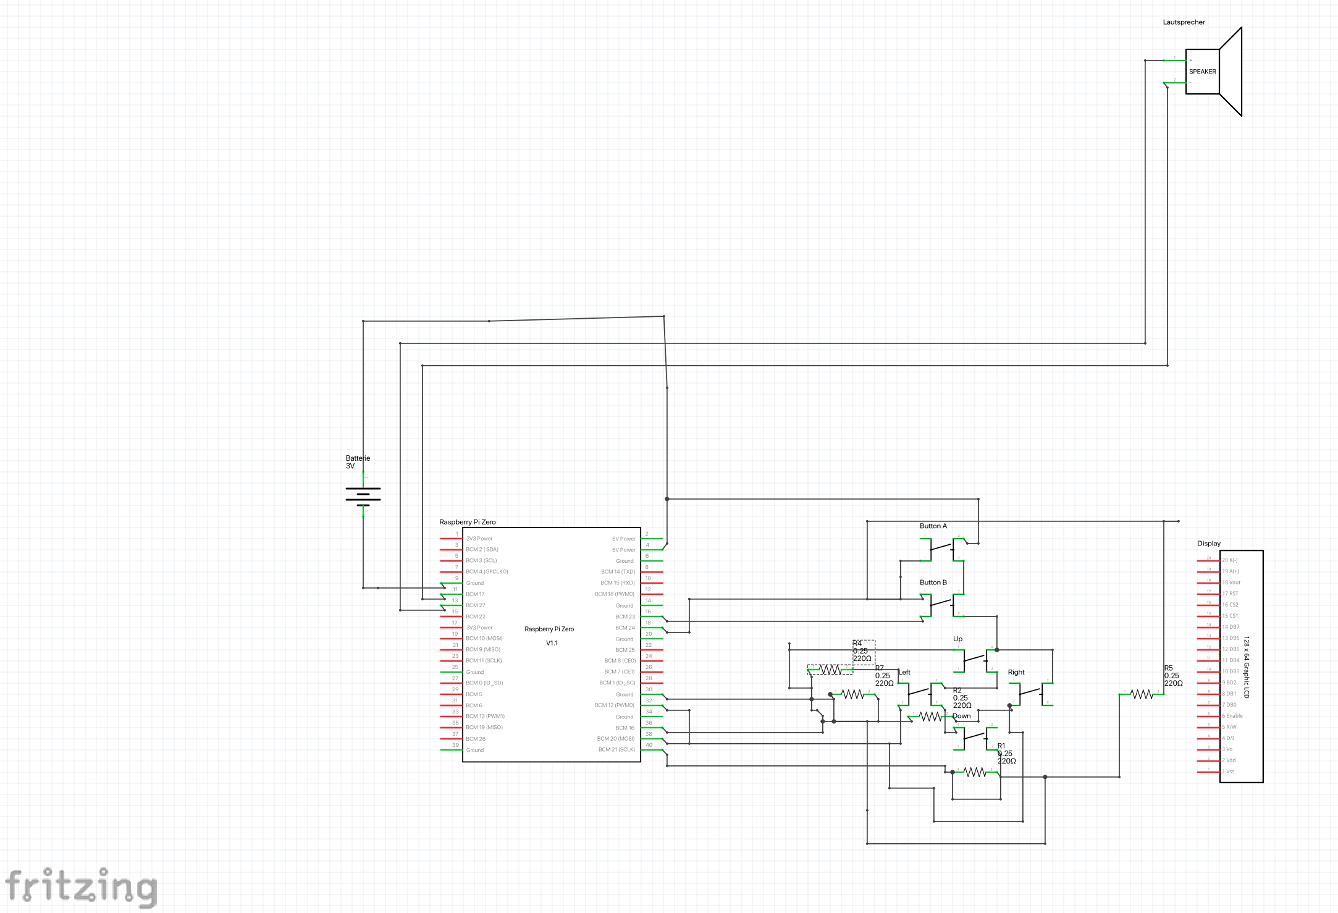
content/posts/pictures/Schaltplan.png
