ManuelaDragic/sketchingWithHardware/content/posts/pictures/Schaltung.png

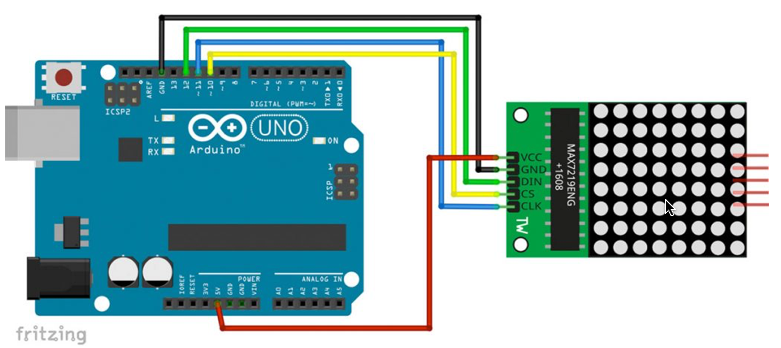
content/posts/pictures/Schaltung.png
