ManuelaDragic/sketchingWithHardware/content/posts/pictures/schritt3.jpeg

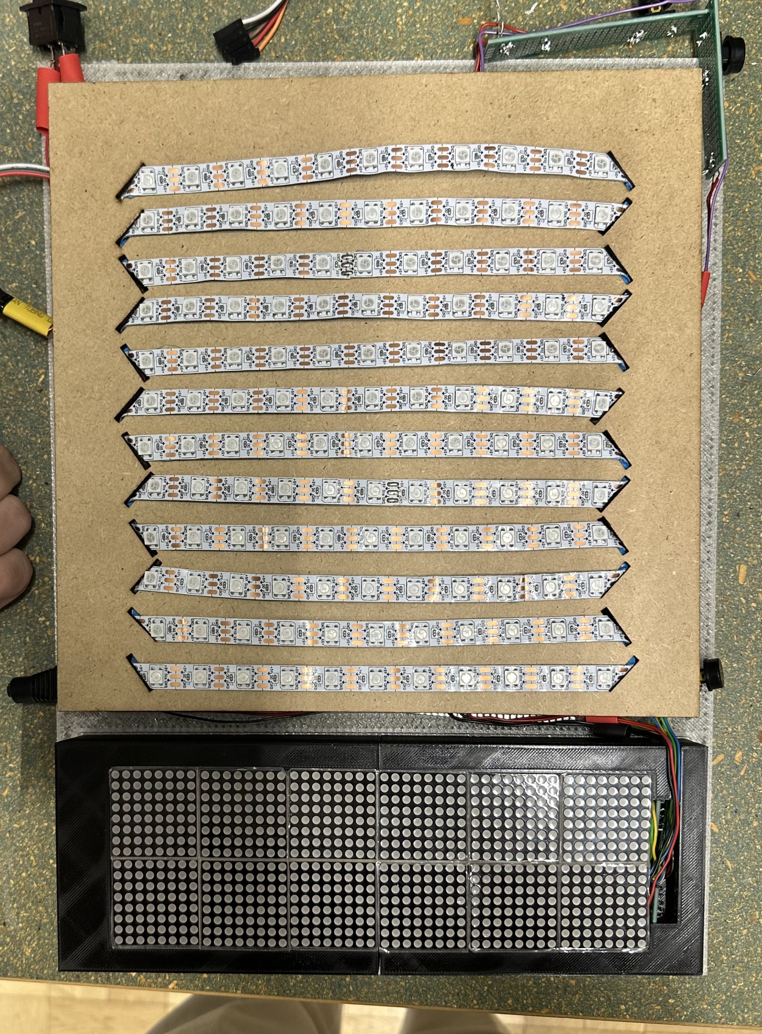
content/posts/pictures/schritt3.jpeg
