ManuelaDragic/sketchingWithHardware/content/posts/pictures/schritt4.jpeg

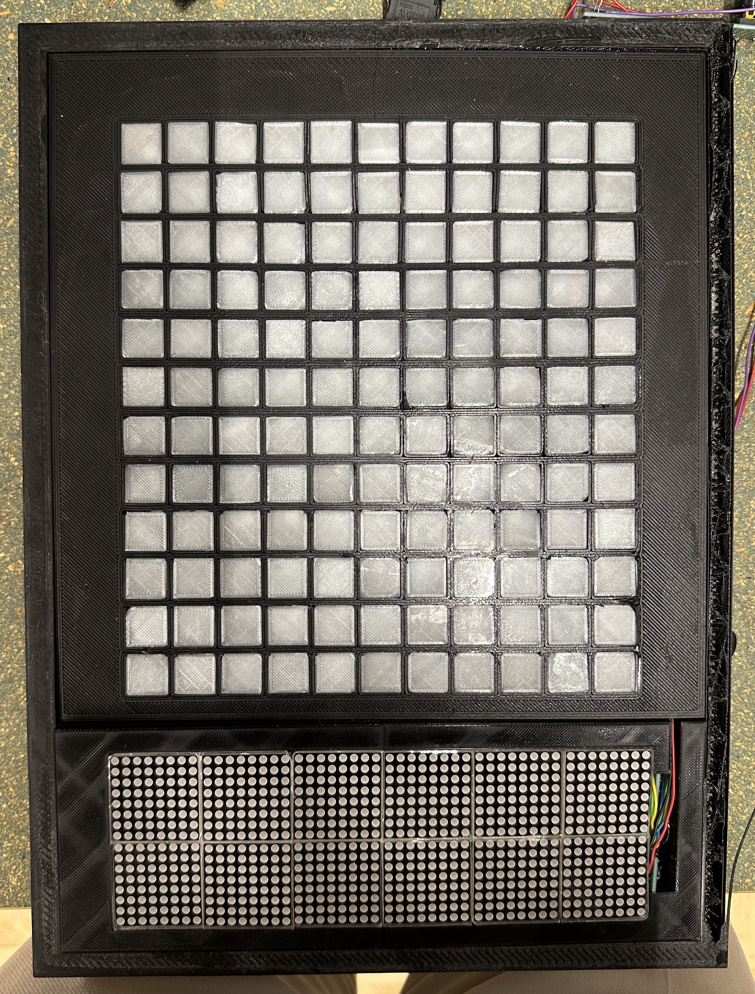
content/posts/pictures/schritt4.jpeg
