ManuelaDragic/sketchingWithHardware/content/posts/pictures/schritt5.jpeg

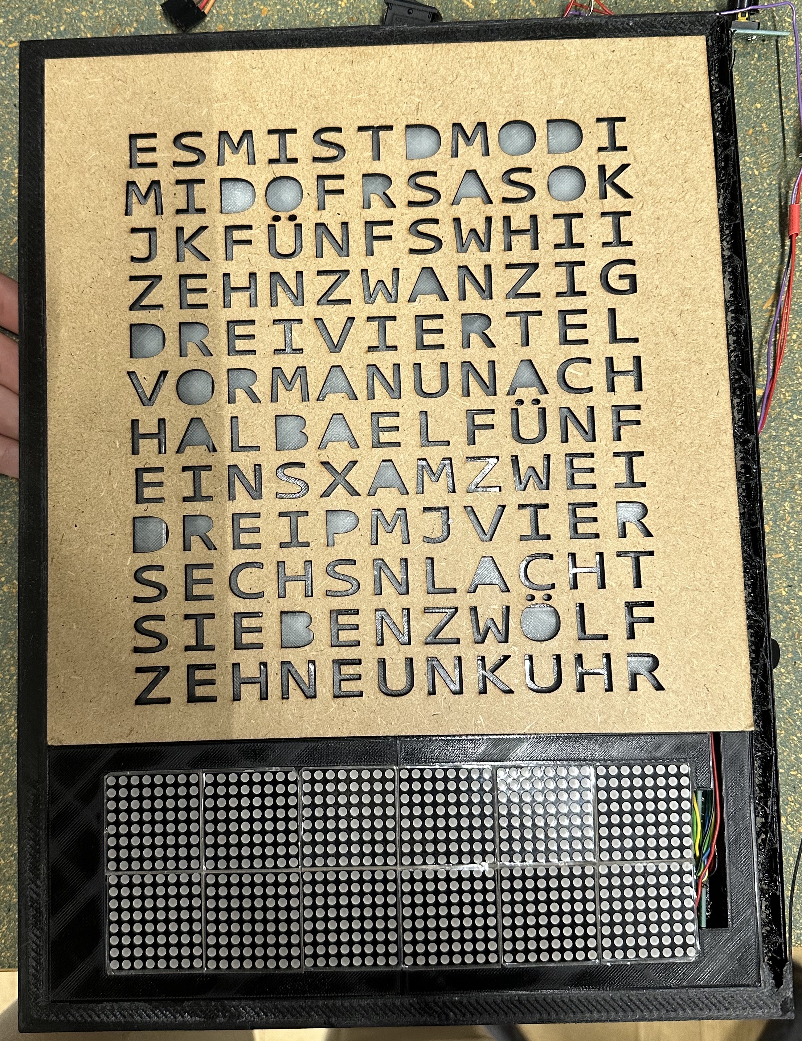
content/posts/pictures/schritt5.jpeg
