ManuelaDragic/sketchingWithHardware/content/posts/pictures/Schubkurbel.jpeg

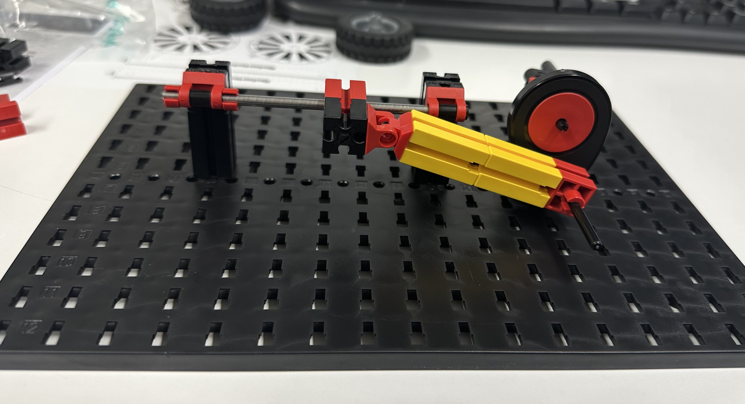
content/posts/pictures/Schubkurbel.jpeg
