ManuelaDragic/sketchingWithHardware/content/posts/pictures/skizze1.jpg

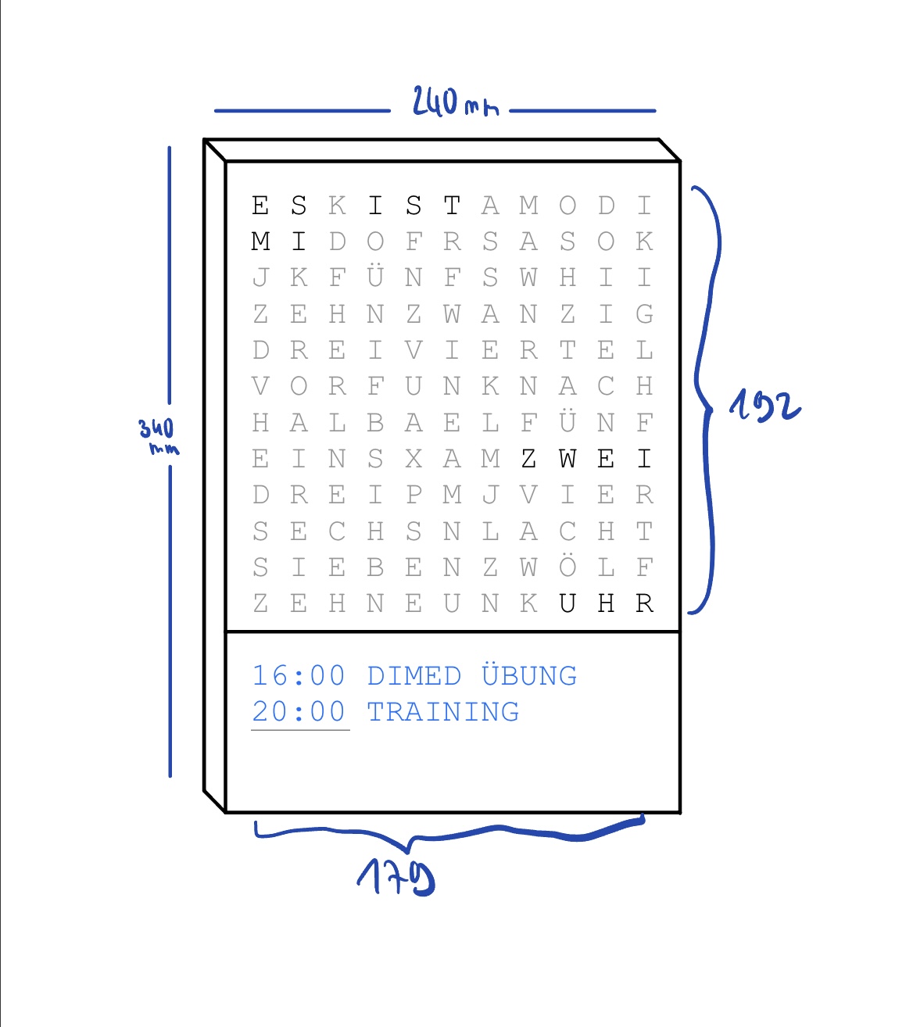
content/posts/pictures/skizze1.jpg
