ManuelaDragic/sketchingWithHardware/content/posts/pictures/Skizze1.png

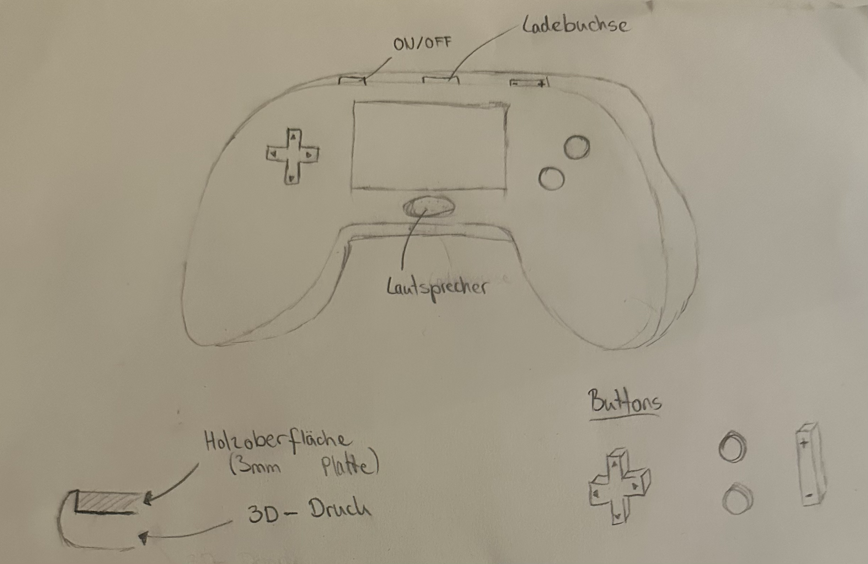
content/posts/pictures/Skizze1.png
