ManuelaDragic/sketchingWithHardware/content/posts/pictures/skizze2.jpg

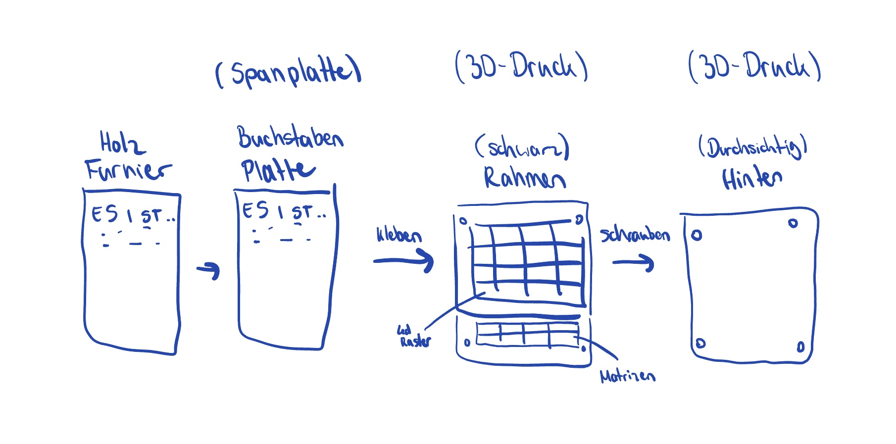
content/posts/pictures/skizze2.jpg
