ManuelaDragic/sketchingWithHardware/content/posts/pictures/Skizze2.png

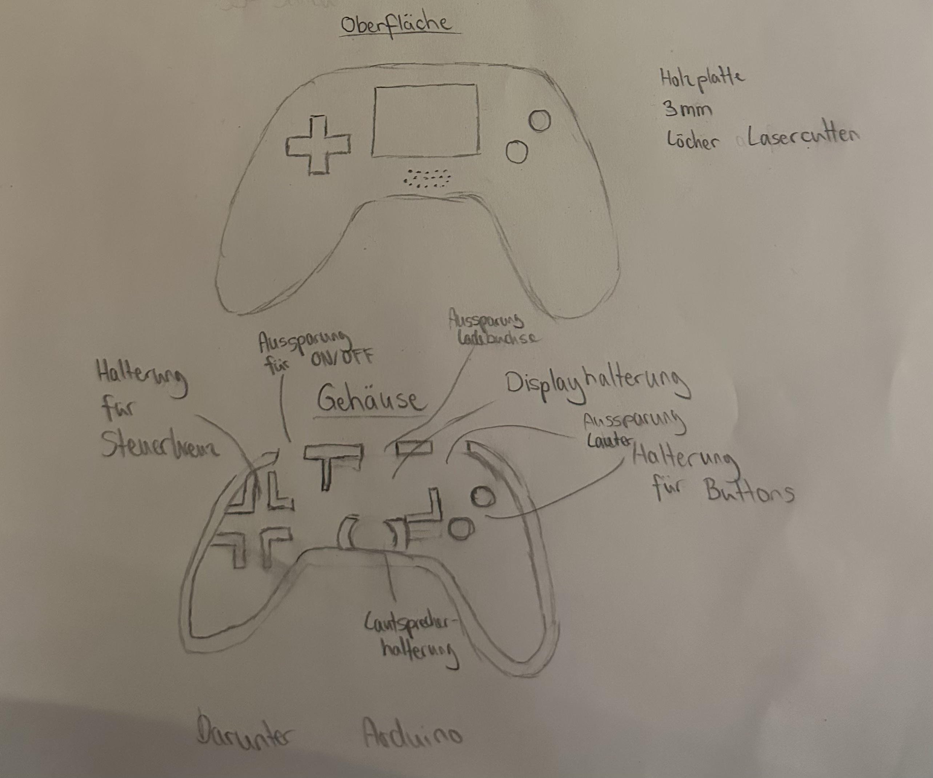
content/posts/pictures/Skizze2.png
