ManuelaDragic/sketchingWithHardware/content/posts/pictures/Steckplatine.png

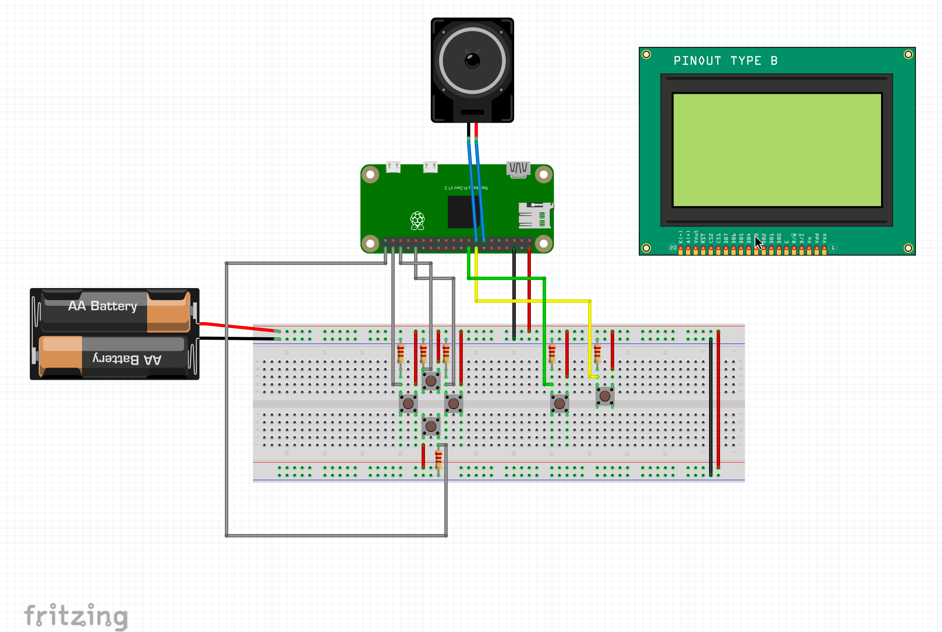
content/posts/pictures/Steckplatine.png
