ManuelaDragic/sketchingWithHardware/content/posts/pictures/Verkabelung.jpg

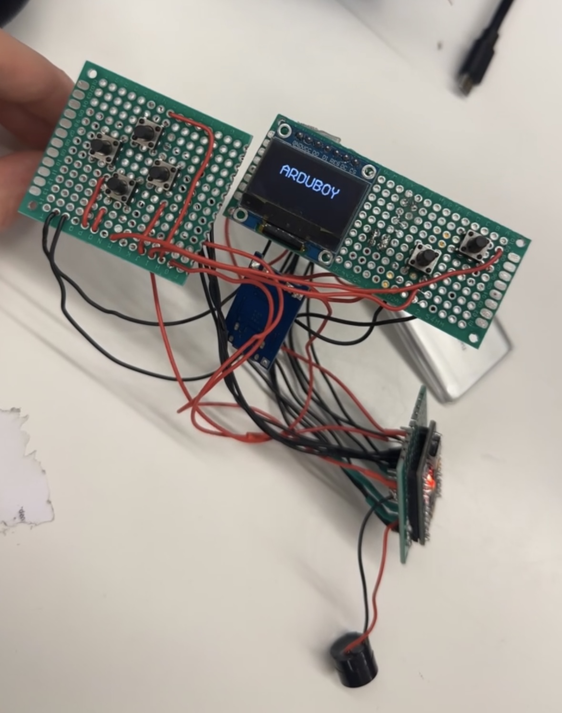
content/posts/pictures/Verkabelung.jpg
