ManuelaDragic/sketchingWithHardware/content/posts/pictures/widerstaende.jpg

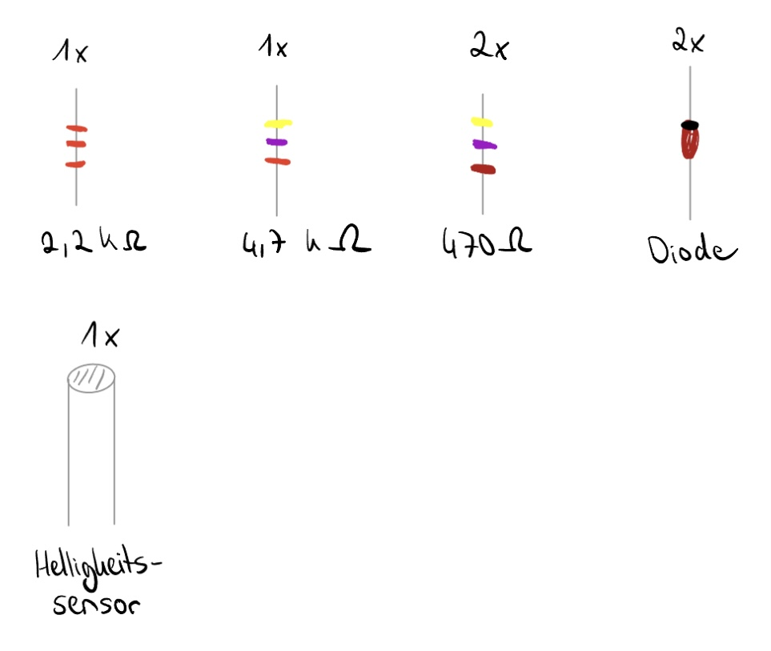
content/posts/pictures/widerstaende.jpg
