ManuelaDragic/sketchingWithHardware/content/posts/pictures/Wordclock.jpeg

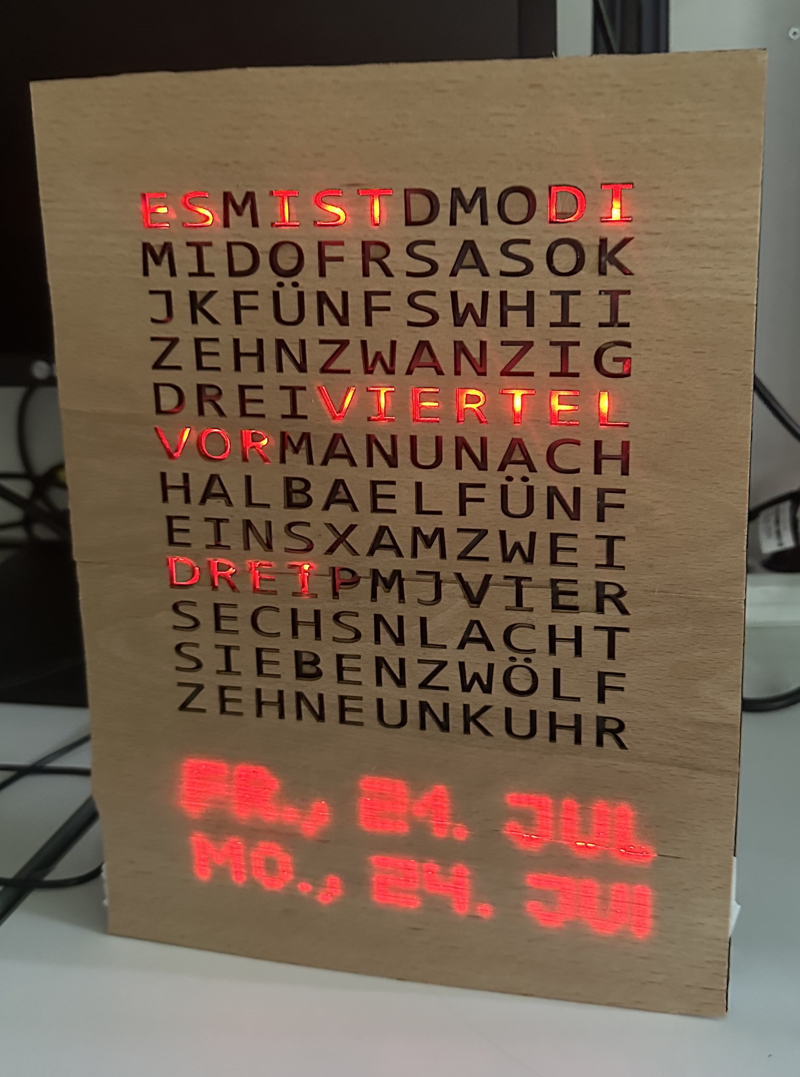
content/posts/pictures/Wordclock.jpeg
