ManuelaDragic/sketchingWithHardware/content/posts/pictures/WordClock.jpg

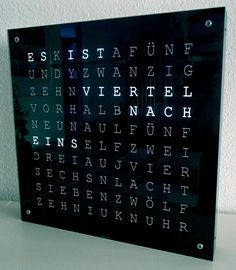
content/posts/pictures/WordClock.jpg
