ManuelaDragic/sketchingWithHardware/content/posts/pictures/WordClockanizer_Plakat.png

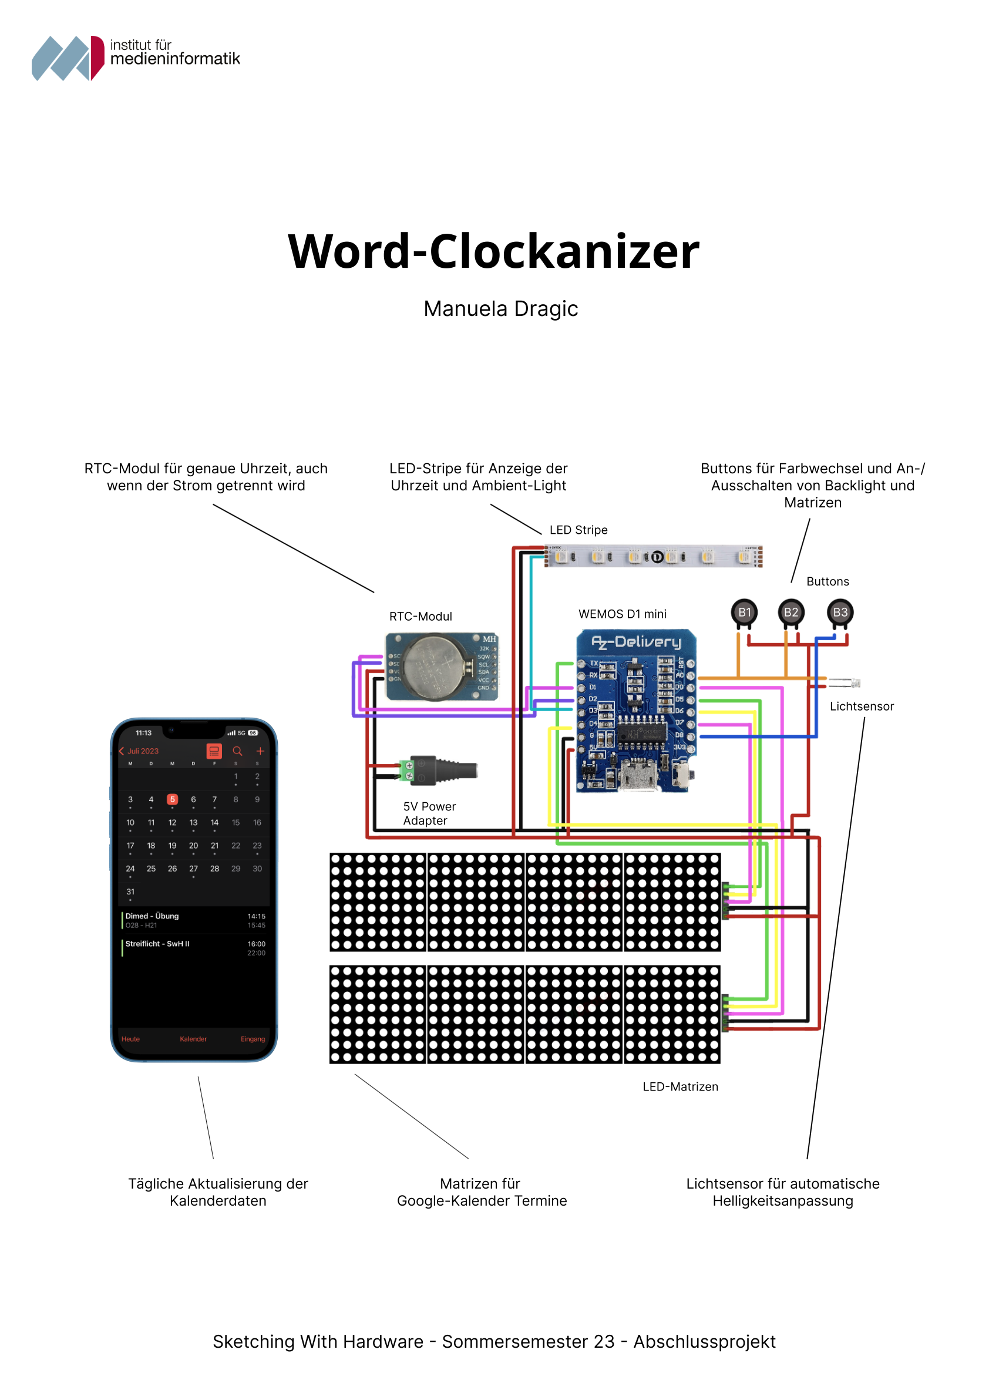
content/posts/pictures/WordClockanizer_Plakat.png
