ManuelaDragic/sketchingWithHardware/static/pictures/additive.jpeg

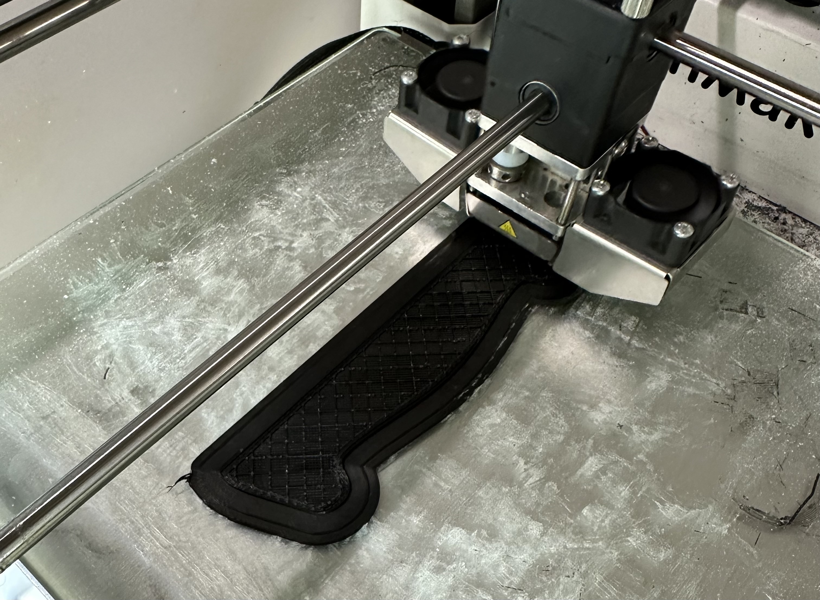
static/pictures/additive.jpeg
