ManuelaDragic/sketchingWithHardware/static/pictures/etechnik.jpeg

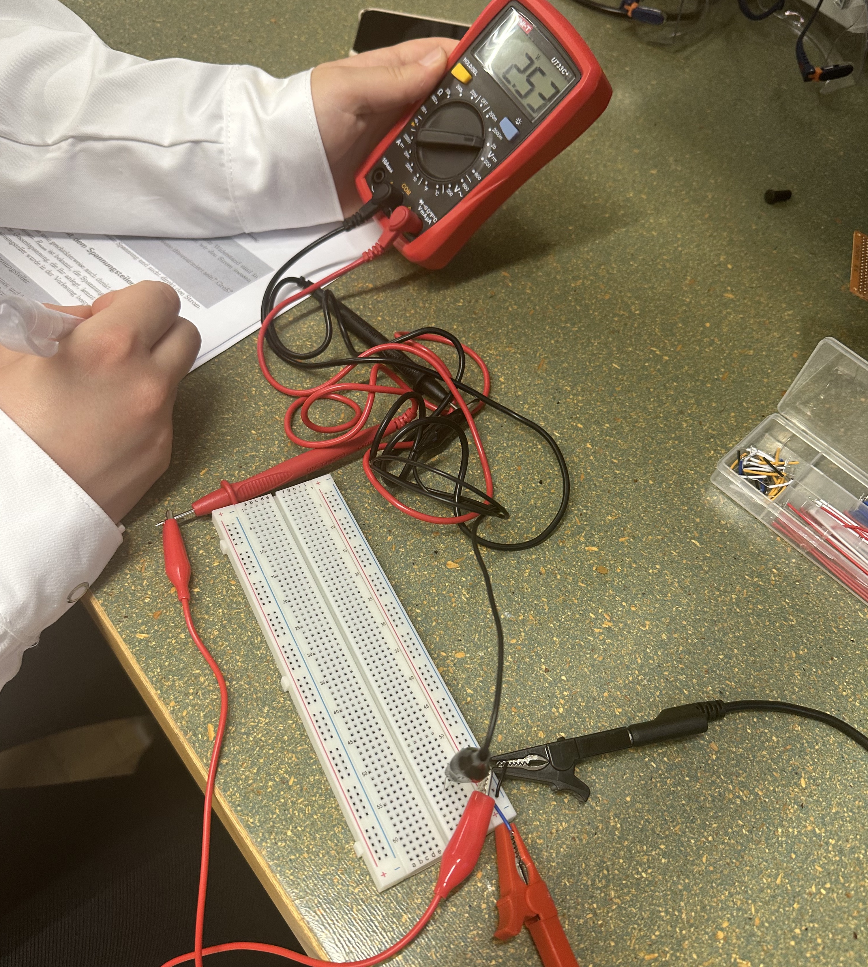
static/pictures/etechnik.jpeg
