ManuelaDragic/sketchingWithHardware/static/pictures/hintergrund.jpeg

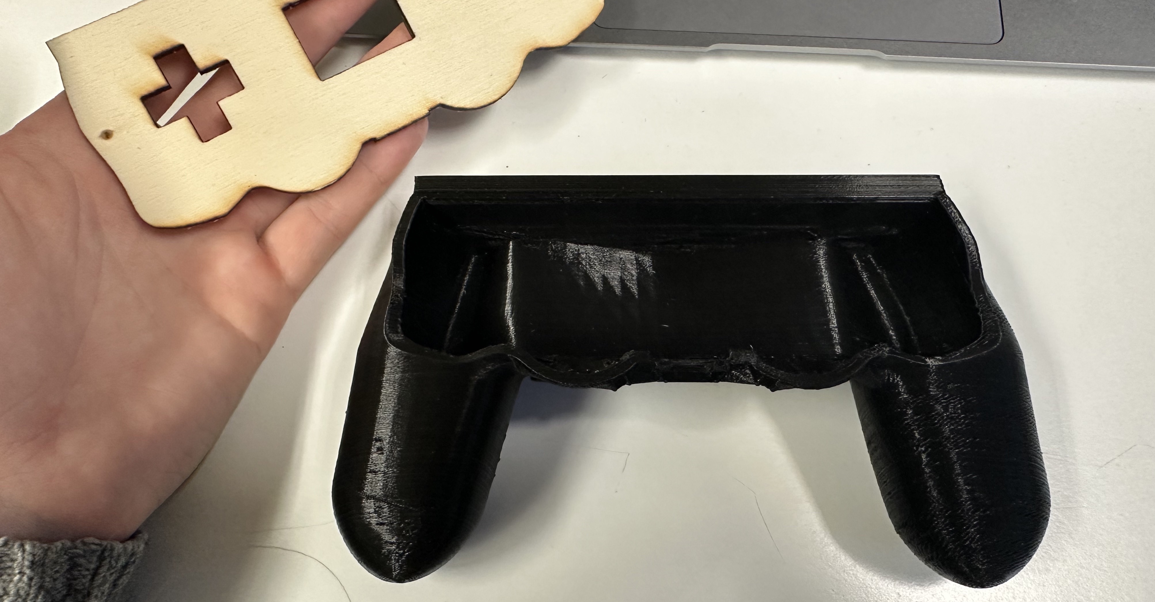
static/pictures/hintergrund.jpeg
