ManuelaDragic/sketchingWithHardware/static/pictures/loeten.jpeg

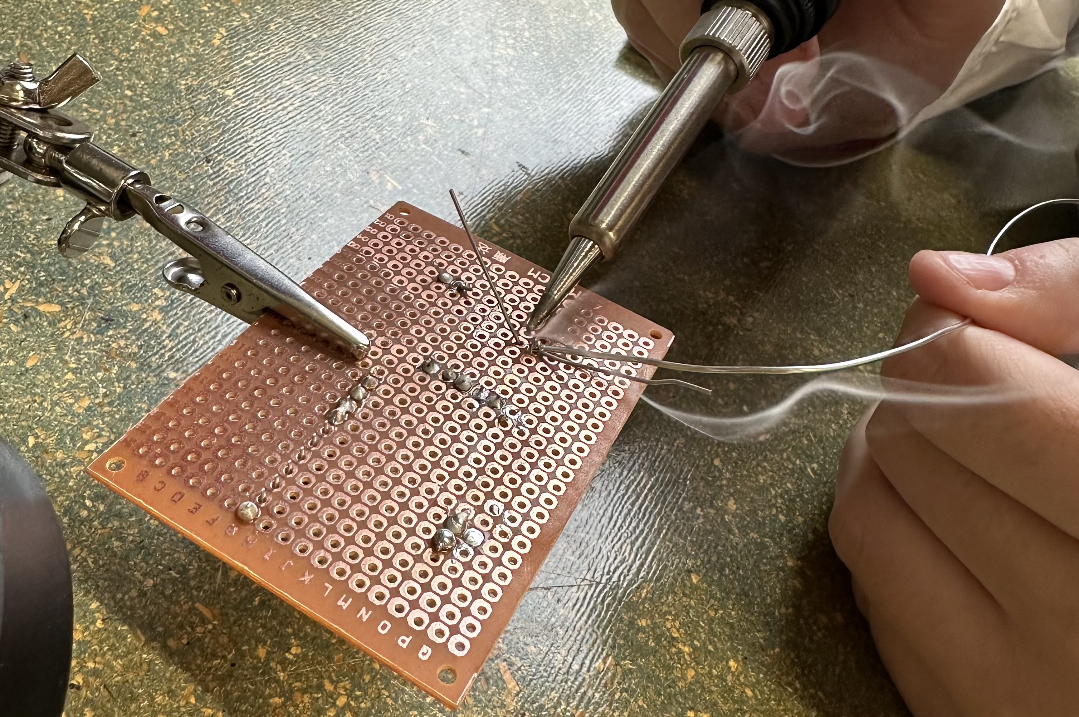
static/pictures/loeten.jpeg
