ManuelaDragic/sketchingWithHardware/static/pictures/mechanik.jpg

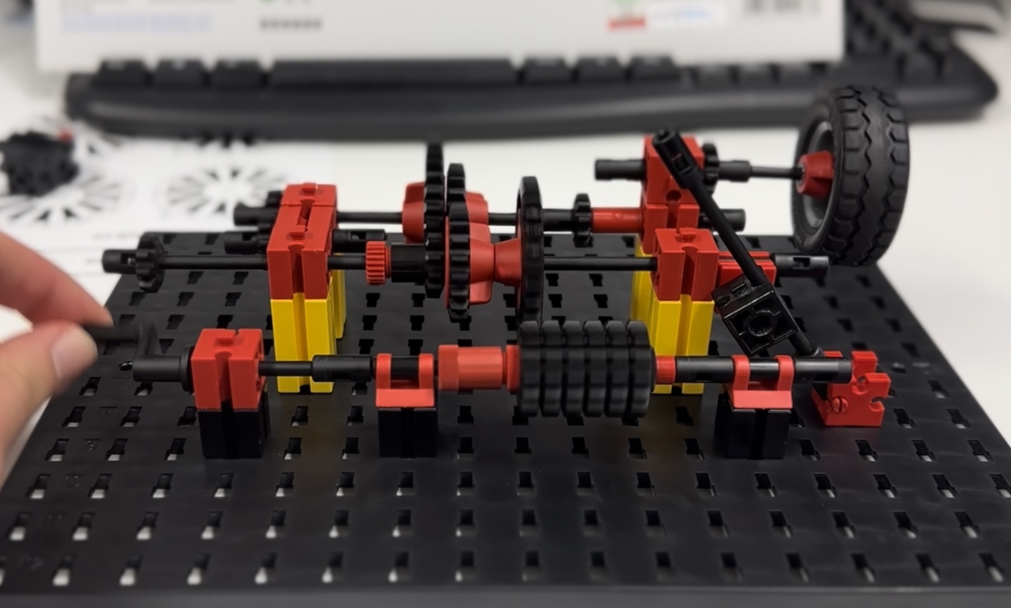
static/pictures/mechanik.jpg
