ManuelaDragic/sketchingWithHardware/static/pictures/microcontroller.jpeg

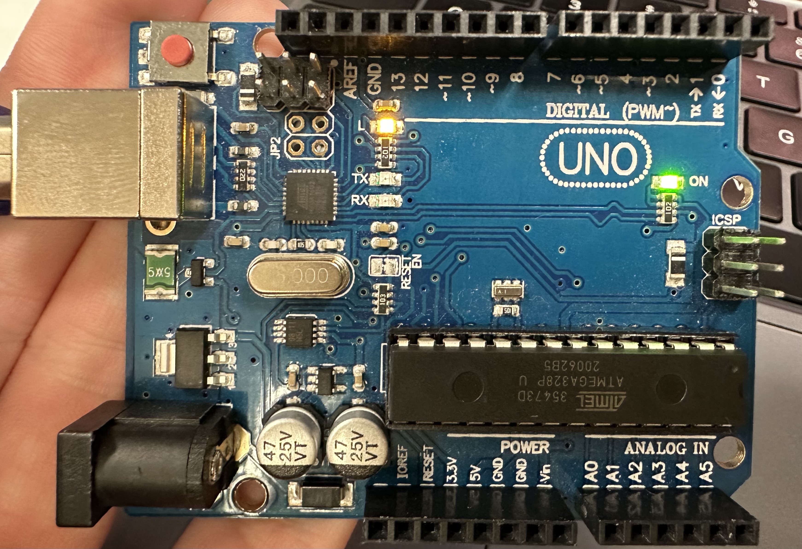
static/pictures/microcontroller.jpeg
