ManuelaDragic/sketchingWithHardware/static/pictures/subtraktive.jpeg

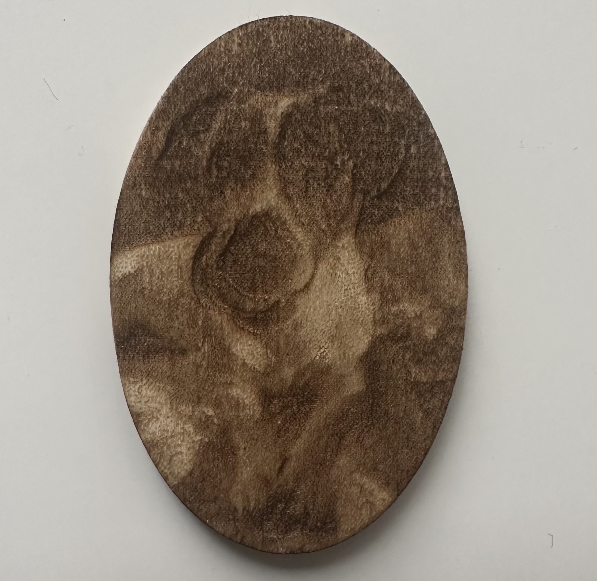
static/pictures/subtraktive.jpeg
