ManuelaDragic/sketchingWithHardware/static/pictures/wordclock.jpeg

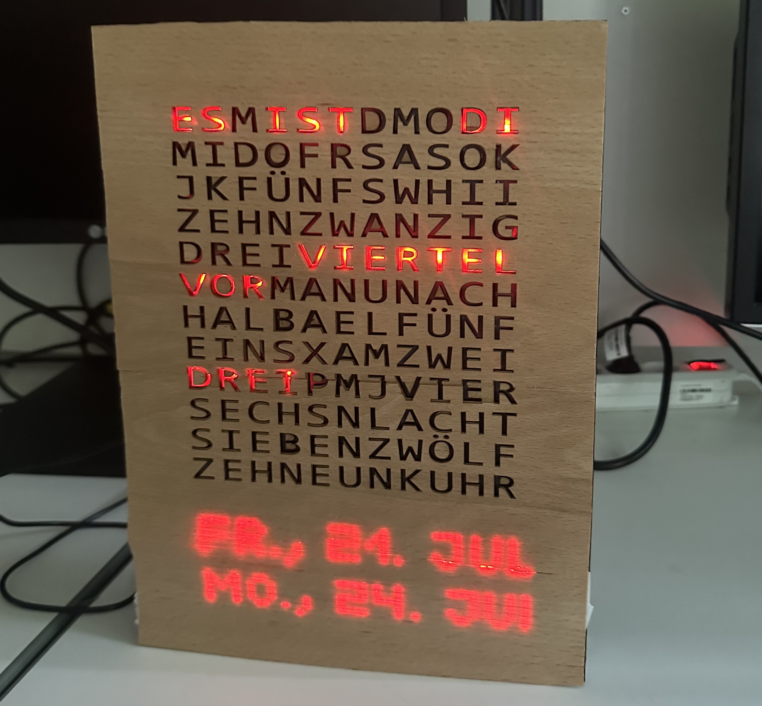
static/pictures/wordclock.jpeg
