ManuelaDragic/sketchingWithHardware/content/posts/pictures/aufbau.jpg

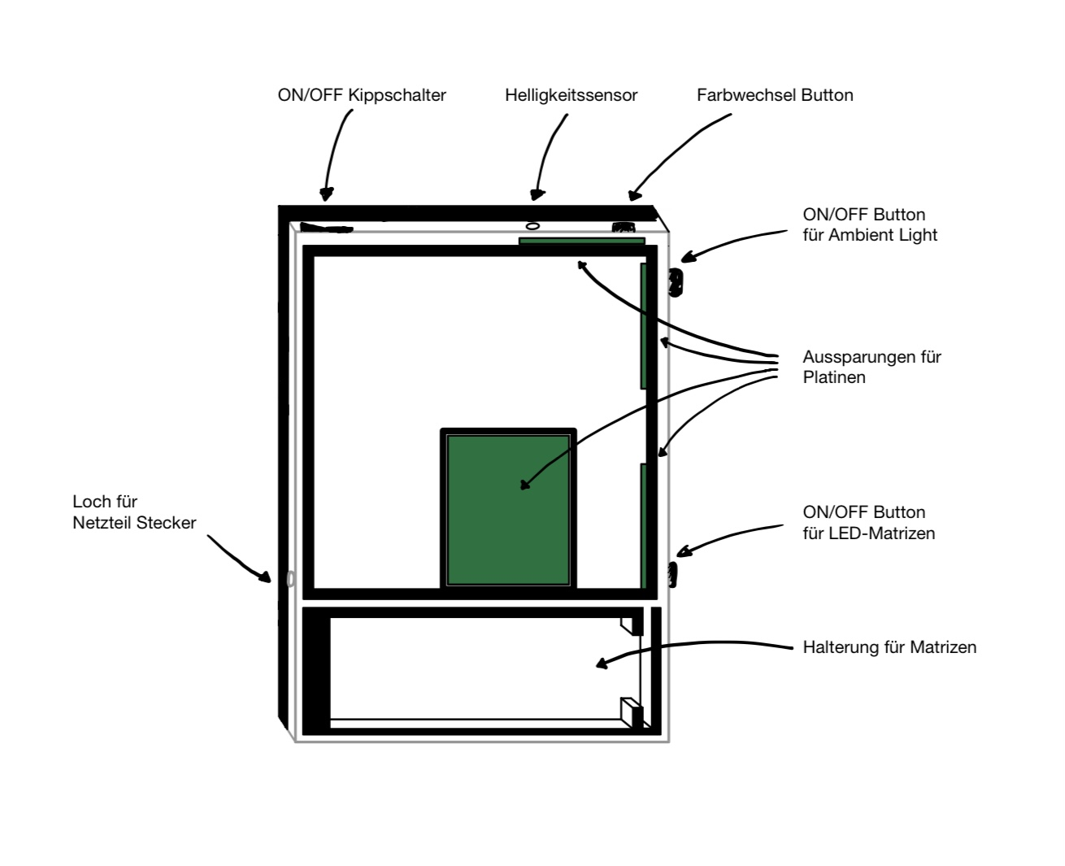
content/posts/pictures/aufbau.jpg
