ManuelaDragic/sketchingWithHardware/code/WordClock/WordClockFont.h

// user defined font
#pragma once

MD_MAX72XX::fontType_t WordClockFont[] PROGMEM = 
{
	0, 	// 0
	0, 	// 1
	0, 	// 2
	0, 	// 3
	0, 	// 4
	0, 	// 5
	0, 	// 6
	0, 	// 7
	0, 	// 8
	0, 	// 9
	0, 	// 10
	0, 	// 11
	0, 	// 12
	0, 	// 13
	0, 	// 14
	0, 	// 15
	0, 	// 16
	0, 	// 17
	0, 	// 18
	0, 	// 19
	0, 	// 20
	0, 	// 21
	0, 	// 22
	0, 	// 23
	0, 	// 24
	0, 	// 25
	0, 	// 26
	0, 	// 27
	0, 	// 28
	0, 	// 29
	0, 	// 30
	0, 	// 31
	2, 0, 0, 	// 32
	1, 23, 	// 33
	3, 7, 0, 7, 	// 34
	5, 10, 31, 10, 31, 10, 	// 35
	5, 18, 21, 31, 21, 9, 	// 36
	5, 19, 11, 4, 26, 25, 	// 37
	4, 10, 21, 10, 16, 	// 38
	1, 7, 	// 39
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
};
