ManuelaDragic/sketchingWithHardware/content/posts/pictures/buchstabenplatte.jpeg

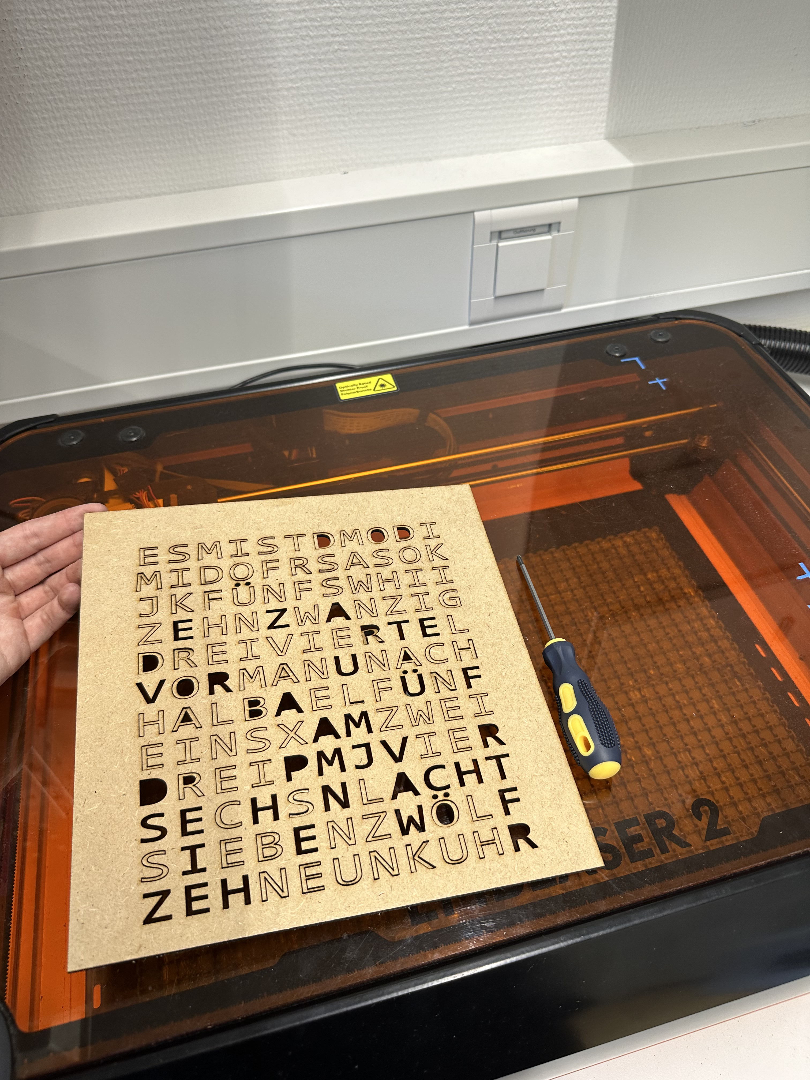
content/posts/pictures/buchstabenplatte.jpeg
