ManuelaDragic/sketchingWithHardware/content/posts/pictures/furnier.jpeg

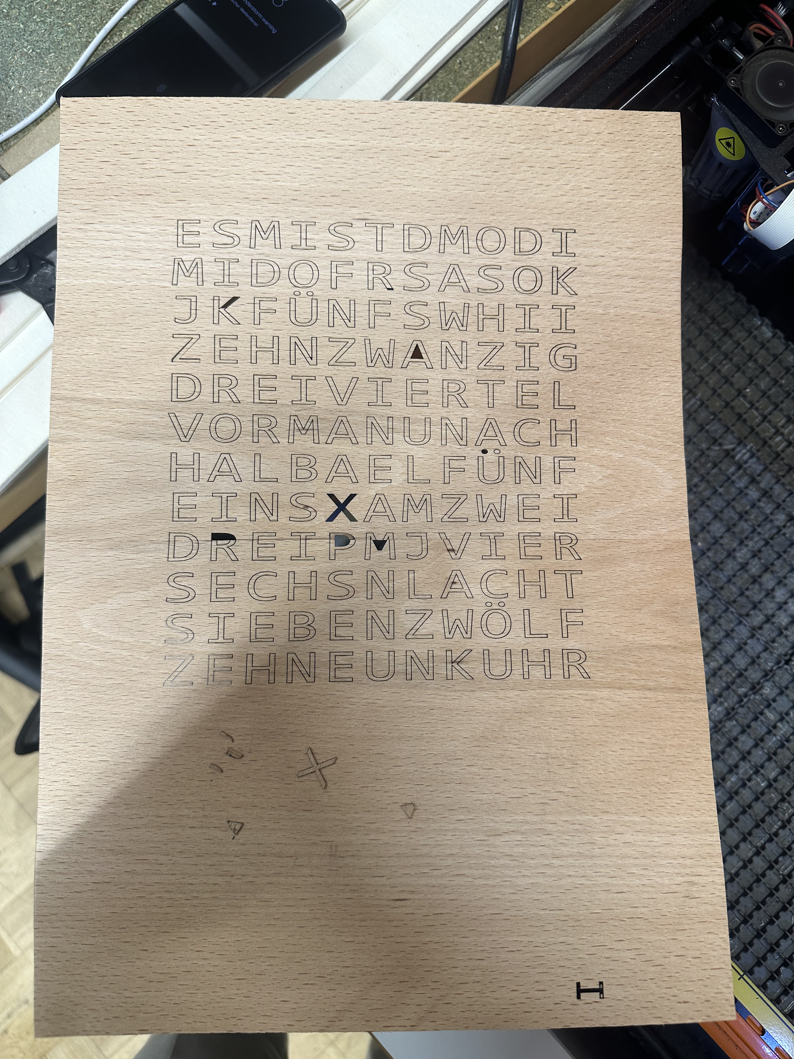
content/posts/pictures/furnier.jpeg
