ManuelaDragic/sketchingWithHardware/content/posts/pictures/innenseite.jpeg

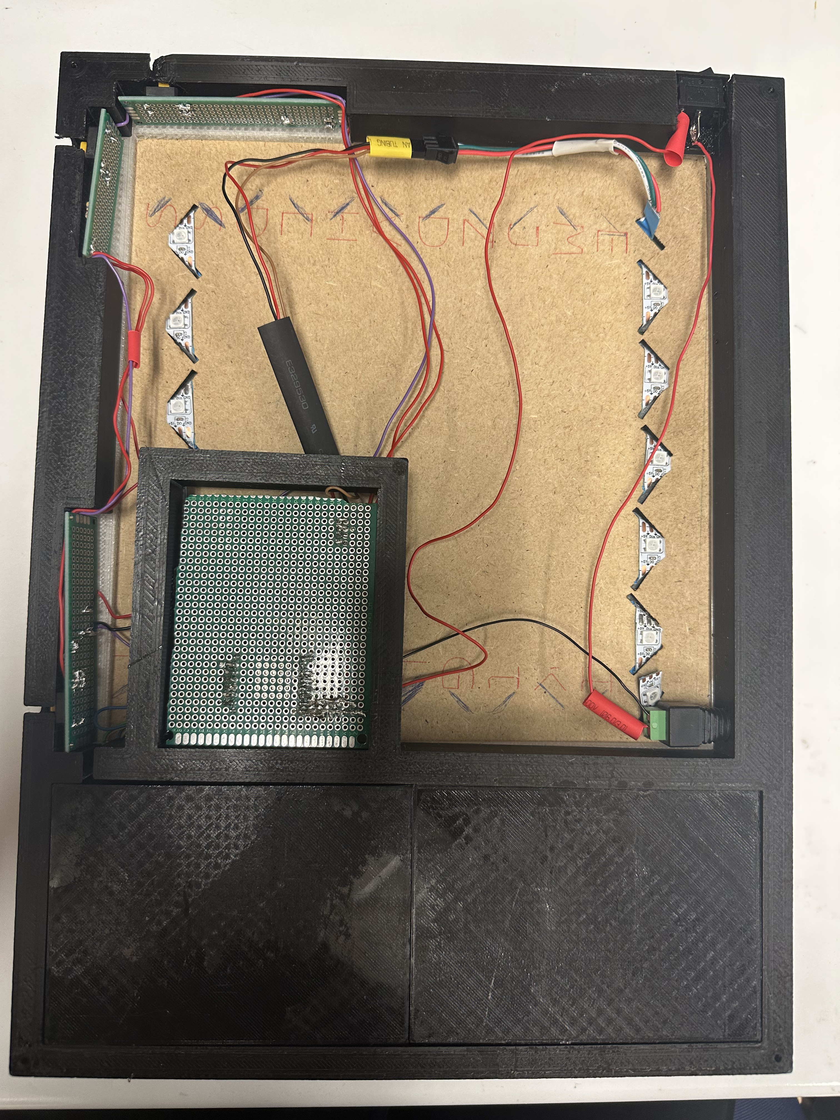
content/posts/pictures/innenseite.jpeg
