ManuelaDragic/sketchingWithHardware/content/posts/pictures/lasercut2.jpeg

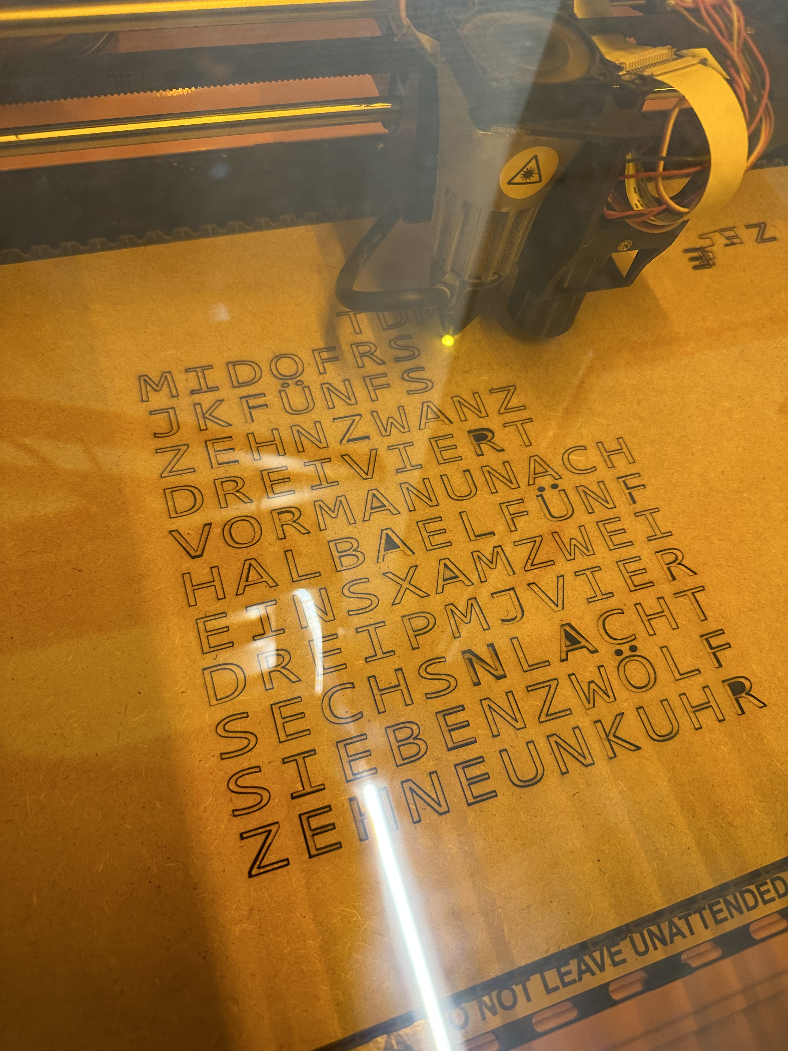
content/posts/pictures/lasercut2.jpeg
