ManuelaDragic/sketchingWithHardware/content/posts/pictures/schritt2.jpeg

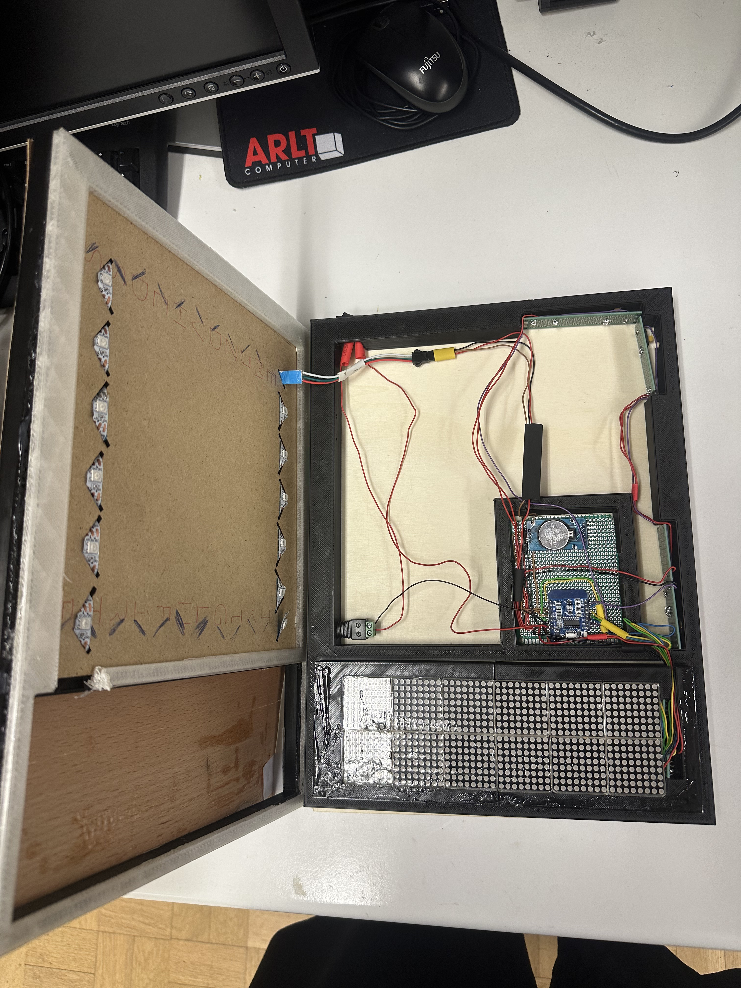
content/posts/pictures/schritt2.jpeg
